slacky1965/air_quality_monitor_zrd/doc/images/screen90.jpg

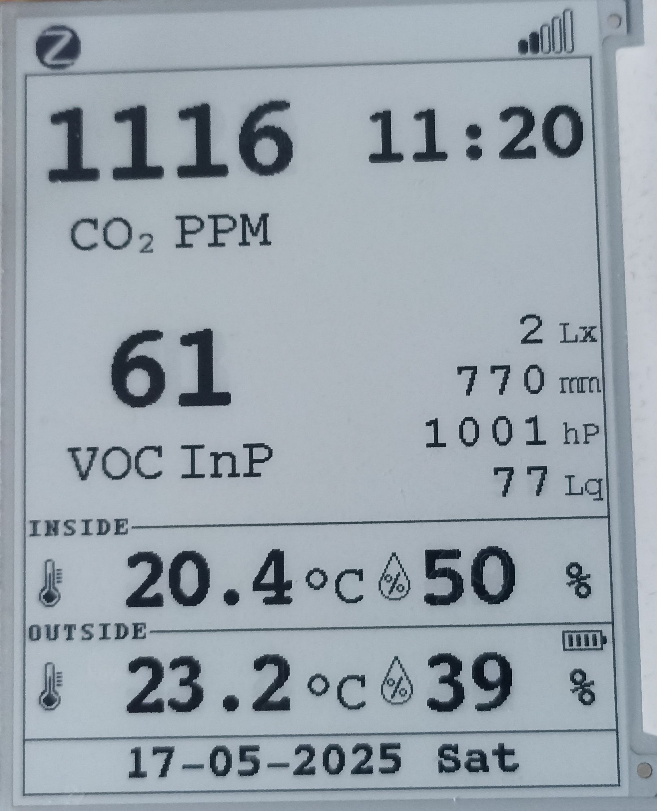
doc/images/screen90.jpg
