slacky1965/air_quality_monitor_zrd/doc/images/z2m_exposes_set1.jpg

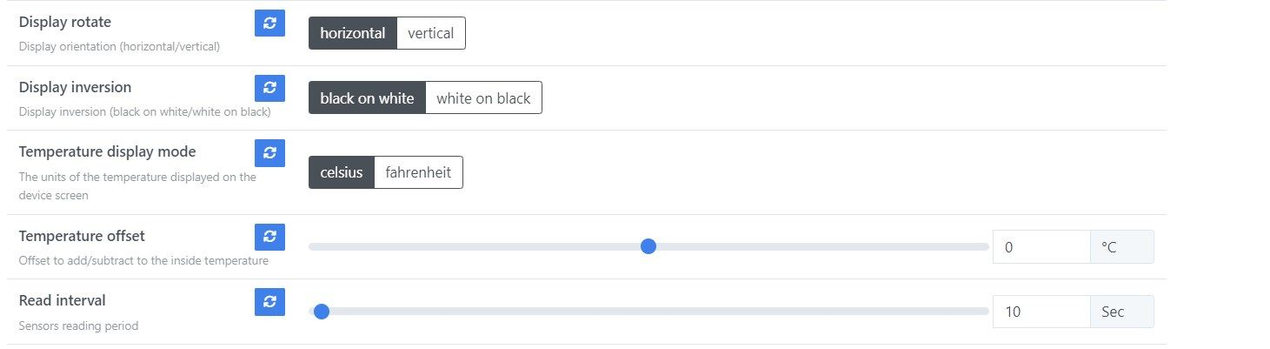
doc/images/z2m_exposes_set1.jpg
