slacky1965/air_quality_monitor_zrd/src/epaper/roboto_font30.c

#include "epdfont.h"

//
//  Font data for Roboto 30pt
//

// Character bitmaps for Roboto 30pt
const uint8_t roboto_font30_Table[] =
{
    // @0 ' ' (33 pixels wide)
    0x00, 0x00, 0x00, 0x00, 0x00, //
    0x00, 0x00, 0x00, 0x00, 0x00, //
    0x00, 0x00, 0x00, 0x00, 0x00, //
    0x00, 0x00, 0x00, 0x00, 0x00, //
    0x00, 0x00, 0x00, 0x00, 0x00, //
    0x00, 0x00, 0x00, 0x00, 0x00, //
    0x00, 0x00, 0x00, 0x00, 0x00, //
    0x00, 0x00, 0x00, 0x00, 0x00, //
    0x00, 0x00, 0x00, 0x00, 0x00, //
    0x00, 0x00, 0x00, 0x00, 0x00, //
    0x00, 0x00, 0x00, 0x00, 0x00, //
    0x00, 0x00, 0x00, 0x00, 0x00, //
    0x00, 0x00, 0x00, 0x00, 0x00, //
    0x00, 0x00, 0x00, 0x00, 0x00, //
    0x00, 0x00, 0x00, 0x00, 0x00, //
    0x00, 0x00, 0x00, 0x00, 0x00, //
    0x00, 0x00, 0x00, 0x00, 0x00, //
    0x00, 0x00, 0x00, 0x00, 0x00, //
    0x00, 0x00, 0x00, 0x00, 0x00, //
    0x00, 0x00, 0x00, 0x00, 0x00, //
    0x00, 0x00, 0x00, 0x00, 0x00, //
    0x00, 0x00, 0x00, 0x00, 0x00, //
    0x00, 0x00, 0x00, 0x00, 0x00, //
    0x00, 0x00, 0x00, 0x00, 0x00, //
    0x00, 0x00, 0x00, 0x00, 0x00, //
    0x00, 0x00, 0x00, 0x00, 0x00, //
    0x00, 0x00, 0x00, 0x00, 0x00, //
    0x00, 0x00, 0x00, 0x00, 0x00, //
    0x00, 0x00, 0x00, 0x00, 0x00, //
    0x00, 0x00, 0x00, 0x00, 0x00, //
    0x00, 0x00, 0x00, 0x00, 0x00, //
    0x00, 0x00, 0x00, 0x00, 0x00, //
    0x00, 0x00, 0x00, 0x00, 0x00, //
    0x00, 0x00, 0x00, 0x00, 0x00, //
    0x00, 0x00, 0x00, 0x00, 0x00, //
    0x00, 0x00, 0x00, 0x00, 0x00, //
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
    0x00, 0x00, 0x00, 0x00, 0x00, //
    0x00, 0x00, 0x00, 0x00, 0x00, //
    0x00, 0x00, 0x00, 0x00, 0x00, //
    0x00, 0x00, 0x00, 0x00, 0x00, //
    0x00, 0x00, 0x00, 0x00, 0x00, //
    0x00, 0x00, 0x00, 0x00, 0x00, //
    0x00, 0x00, 0x00, 0x00, 0x00, //
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
