slacky1965/air_quality_monitor_zrd/src/zcl_appCb.c

/********************************************************************************************************
 * @file    zcl_appCb.c
 *
 * @brief   This is the source file for zcl_appCb
 *
 * @author  Zigbee Group
 * @date    2021
 *
 * @par     Copyright (c) 2021, Telink Semiconductor (Shanghai) Co., Ltd. ("TELINK")
 *			All rights reserved.
 *
 *          Licensed under the Apache License, Version 2.0 (the "License");
 *          you may not use this file except in compliance with the License.
 *          You may obtain a copy of the License at
 *
 *              http://www.apache.org/licenses/LICENSE-2.0
 *
 *          Unless required by applicable law or agreed to in writing, software
 *          distributed under the License is distributed on an "AS IS" BASIS,
 *          WITHOUT WARRANTIES OR CONDITIONS OF ANY KIND, either express or implied.
 *          See the License for the specific language governing permissions and
 *          limitations under the License.
 *
 *******************************************************************************************************/

/**********************************************************************
 * INCLUDES
 */
#include "tl_common.h"
#include "zcl_include.h"

#include "app_main.h"


/**********************************************************************
 * LOCAL CONSTANTS
 */


/**********************************************************************
 * TYPEDEFS
 */


/**********************************************************************
 * LOCAL FUNCTIONS
 */
#ifdef ZCL_READ
static void app_zclReadRspCmd(uint16_t clusterId, zclReadRspCmd_t *pReadRspCmd);
#endif
#ifdef ZCL_WRITE
static void app_zclWriteRspCmd(uint16_t clusterId, zclWriteRspCmd_t *pWriteRspCmd);
static void app_zclWriteReqCmd(uint8_t endPoint, uint16_t clusterId, zclWriteCmd_t *pWriteReqCmd);
#endif
#ifdef ZCL_REPORT
static void app_zclCfgReportCmd(uint8_t endPoint, uint16_t clusterId, zclCfgReportCmd_t *pCfgReportCmd);
static void app_zclCfgReportRspCmd(uint16_t clusterId, zclCfgReportRspCmd_t *pCfgReportRspCmd);
static void app_zclReportCmd(uint16_t clusterId, zclReportCmd_t *pReportCmd, aps_data_ind_t aps_data_ind);
#endif
static void app_zclDfltRspCmd(uint16_t clusterId, zclDefaultRspCmd_t *pDftRspCmd);
static void app_displayMoveToLevelProcess(uint8_t endpoint, uint8_t cmdId, moveToLvl_t *cmd);

/**********************************************************************
 * GLOBAL VARIABLES
 */


/**********************************************************************
 * LOCAL VARIABLES
 */
#ifdef ZCL_IDENTIFY
static ev_timer_event_t *identifyTimerEvt = NULL;
#endif

/**********************************************************************
 * FUNCTIONS
 */

/*********************************************************************
 * @fn      app_zclProcessIncomingMsg
 *
 * @brief   Process ZCL Foundation incoming message.
 *
 * @param   pInMsg - pointer to the received message
 *
 * @return  None
 */
void app_zclProcessIncomingMsg(zclIncoming_t *pInHdlrMsg)
{
//    printf("app_zclProcessIncomingMsg(). hdr.cmd: 0x%x\r\n", pInHdlrMsg->hdr.cmd);

	uint16_t cluster = pInHdlrMsg->msg->indInfo.cluster_id;
	uint8_t endPoint = pInHdlrMsg->msg->indInfo.dst_ep;
	aps_data_ind_t aps_data_ind = pInHdlrMsg->msg->indInfo;
//	uint16_t addr = pInHdlrMsg->msg->indInfo.src_short_addr;

	switch(pInHdlrMsg->hdr.cmd)
	{
#ifdef ZCL_READ
		case ZCL_CMD_READ_RSP:
			app_zclReadRspCmd(cluster, pInHdlrMsg->attrCmd);
			break;
#endif
#ifdef ZCL_WRITE
		case ZCL_CMD_WRITE_RSP:
			app_zclWriteRspCmd(cluster, pInHdlrMsg->attrCmd);
			break;
		case ZCL_CMD_WRITE:
		    app_zclWriteReqCmd(endPoint, cluster, pInHdlrMsg->attrCmd);
			break;
#endif
#ifdef ZCL_REPORT
		case ZCL_CMD_CONFIG_REPORT:
			app_zclCfgReportCmd(endPoint, cluster, pInHdlrMsg->attrCmd);
			break;
		case ZCL_CMD_CONFIG_REPORT_RSP:
			app_zclCfgReportRspCmd(cluster, pInHdlrMsg->attrCmd);
			break;
		case ZCL_CMD_REPORT:
			app_zclReportCmd(cluster, pInHdlrMsg->attrCmd, aps_data_ind);
			break;
#endif
		case ZCL_CMD_DEFAULT_RSP:
			app_zclDfltRspCmd(cluster, pInHdlrMsg->attrCmd);
			break;
		default:
			break;
	}
}

#ifdef ZCL_READ
/*********************************************************************
 * @fn      app_zclReadRspCmd
 *
 * @brief   Handler for ZCL Read Response command.
 *
 * @param   pInHdlrMsg - incoming message to process
 *
 * @return  None
 */
static void app_zclReadRspCmd(uint16_t clusterId, zclReadRspCmd_t *pReadRspCmd)
{
//    printf("app_zclReadRspCmd\r\n");
    uint8_t numAttr = pReadRspCmd->numAttr;
    zclReadRspStatus_t *attrList = pReadRspCmd->attrList;

//    uint32_t utc;
    uint32_t time_local;
    bool time_sent = false;

    for (uint8_t i = 0; i < numAttr; i++) {
///*        if (attrList[i].attrID == ZCL_ATTRID_TIME && attrList[i].status == ZCL_STA_SUCCESS) {
//            utc = attrList[i].data[0] & 0xff;
//            utc |= (attrList[i].data[1] << 8)  & 0x0000ffff;
//            utc |= (attrList[i].data[2] << 16) & 0x00ffffff;
//            utc |= (attrList[i].data[3] << 24) & 0xffffffff;
//            zcl_setAttrVal(APP_ENDPOINT1, ZCL_CLUSTER_GEN_TIME, ZCL_ATTRID_TIME, (uint8_t*)&utc);
//            time_sent = true;
//#if UART_PRINTF_MODE && DEBUG_TIME
//            printf("Sync UTC:        %d\r\n", utc+UNIX_TIME_CONST);
//#endif
//        } else */
        if (attrList[i].attrID == ZCL_ATTRID_LOCAL_TIME && attrList[i].status == ZCL_STA_SUCCESS) {
            time_local = attrList[i].data[0] & 0xff;
            time_local |= (attrList[i].data[1] << 8)  & 0x0000ffff;
            time_local |= (attrList[i].data[2] << 16) & 0x00ffffff;
            time_local |= (attrList[i].data[3] << 24) & 0xffffffff;
            zcl_setAttrVal(APP_ENDPOINT1, ZCL_CLUSTER_GEN_TIME, ZCL_ATTRID_LOCAL_TIME, (uint8_t*)&time_local);
            time_sent = true;
#if UART_PRINTF_MODE && DEBUG_TIME
            printf("Sync Local Time: %d\r\n", time_local+UNIX_TIME_CONST);
#endif
            ftime_t *ft = get_ftime(time_local);
            ds3231_time_t t;
            if (app_ds3231_get_time(&t) == DS3231_OK) {
                t.year = ft->year;
                t.month = ft->month;
                t.week = ft->wday + 1;
                t.date = ft->day;
                t.hour = ft->hour;
                t.minute = ft->minute;
                t.second = ft->second;
                app_ds3231_set_time(&t);
            }
        }
    }

    if (time_sent) {
        set_time_sent();
    }
}
#endif	/* ZCL_READ */

#ifdef ZCL_WRITE
/*********************************************************************
 * @fn      app_zclWriteRspCmd
 *
 * @brief   Handler for ZCL Write Response command.
 *
 * @param   pInHdlrMsg - incoming message to process
 *
 * @return  None
 */
static void app_zclWriteRspCmd(uint16_t clusterId, zclWriteRspCmd_t *pWriteRspCmd)
{
//    printf("app_zclWriteRspCmd\r\n");

}

/*********************************************************************
 * @fn      app_zclWriteReqCmd
 *
 * @brief   Handler for ZCL Write Request command.
 *
 * @param   pInHdlrMsg - incoming message to process
 *
 * @return  None
 */
static void app_zclWriteReqCmd(uint8_t endPoint, uint16_t clusterId, zclWriteCmd_t *pWriteReqCmd) {
    uint8_t numAttr = pWriteReqCmd->numAttr;
    zclWriteRec_t *attr = pWriteReqCmd->attrList;

    uint8_t val;
    bool save = false;

//    printf("app_zclWriteReqCmd. cluster: 0x%04x\r\n", clusterId);

    if (clusterId == ZCL_CLUSTER_GEN_LEVEL_CONTROL) {
        for (uint16_t i = 0; i < numAttr; i++) {
            if (attr[i].attrID == ZCL_ATTRID_LEVEL_CURRENT_LEVEL) {
                moveToLvl_t cmd;
                cmd.level = attr[i].attrData[0];
                app_displayMoveToLevelProcess(endPoint, ZCL_CMD_LEVEL_MOVE_TO_LEVEL, &cmd);
            }
        }
    }


    if (clusterId == ZCL_CLUSTER_HAVC_USER_INTERFACE_CONFIG) {
        for (uint16_t i = 0; i < numAttr; i++) {
            if (attr[i].attrID == ZCL_ATTRID_HVAC_TEMPERATURE_DISPLAY_MODE) {
                val = attr[i].attrData[0];
                if (val == 0 || val == 1) {
                    printf("Set %s\r\n", val?"Fahrenheit":"Celsius");
                    if (config.d_mode != val) {
                        config.d_mode = val;
                        save = true;
                        epd_update_temperature_display_mode();
                    }
                }
            } else if (attr[i].attrID == ZCL_ATTRID_HVAC_CUSTOM_DISPLAY_ROTATE) {
                val = attr[i].attrData[0];
                if (val == 0 || val == 1) {
                    printf("Rotate set: %s\r\n", val?"Vertical":"Horizontal");
                    if (config.rotate != val) {
                        config.rotate = val;
                        save = true;
                        TL_SCHEDULE_TASK(epd_forceScreenUpdate, NULL);
                    }
                }
            } else if (attr[i].attrID == ZCL_ATTRID_HVAC_CUSTOM_DISPLAY_INVERSION) {
                val = attr[i].attrData[0];
                if (val == 0 || val == 1) {
                    printf("Inversion set: %s\r\n", val?"Black on white":"White on black");
                    if (config.inversion != val) {
                        config.inversion = val;
                        save = true;
                        TL_SCHEDULE_TASK(epd_forceScreenUpdate, NULL);
                    }
                }
            } else if (attr[i].attrID == ZCL_ATTRID_HVAC_CUSTOM_SOUND) {
                val = attr[i].attrData[0];
                if (val == 0 || val == 1) {
                    printf("Sound set: %s\r\n", val?"On":"Off");
                    if (config.sound != val) {
                        config.sound = val;
                        sound_start(4, 20, 100, val?SOUND_INC:SOUND_DEC);
                        epd_screen_varCb(NULL);
                        save = true;
                    }
                }
            } else if (attr[i].attrID == ZCL_ATTRID_HVAC_CUSTOM_FEATURES_SENSORS) {
                uint8_t ret;
                if (attr[i].attrData[0] == FEATURES_CO2_FORCED_CALIBRATION &&
                        !g_appCtx.co2_forced_calibration &&
                        !g_appCtx.co2_factory_reset) {
                    g_appCtx.co2_forced_calibration = 1;
                    ret = app_scd4x_forced_calibration();
                    printf("CO2 calibration: %d, ret: %d\r\n", attr[i].attrData[0], ret);
                } else if (attr[i].attrData[0] == FEATURES_CO2_FACTORY_RESET &&
                        !g_appCtx.co2_factory_reset &&
                        !g_appCtx.co2_forced_calibration) {
                    g_appCtx.co2_factory_reset = 1;
                    ret = app_scd4x_factory_reset();
                    printf("CO2 factory reset: %d, ret: %d\r\n", attr[i].attrData[0], ret);
                } else if (attr[i].attrData[0] == FEATURES_BIND_RESET) {
                    printf("Bind reset: %d\r\n", attr[i].attrData[0]);
                    bind_outside_init();
                }
                uint8_t attrFeatures = 0;
                zcl_setAttrVal(APP_ENDPOINT1, ZCL_CLUSTER_HAVC_USER_INTERFACE_CONFIG,
                               ZCL_ATTRID_HVAC_CUSTOM_FEATURES_SENSORS, (uint8_t*)&attrFeatures);
            }
        }
    }

    if (clusterId == ZCL_CLUSTER_MS_TEMPERATURE_MEASUREMENT) {
        for (uint16_t i = 0; i < numAttr; i++) {
            if (attr[i].attrID == ZCL_ATTRID_TMS_CUSTOM_TEMPERATURE_OFFSET) {
                int16_t temp = attr[i].attrData[0] & 0xff;
                temp |= (attr[i].attrData[1] << 8) & 0xffff;
//                printf("Temperature offset: %d\r\n", temp);
                if (temp >= TEMPERATURE_OFFSET_MIN && temp <= TEMPERATURE_OFFSET_MAX) {
                    if (temp != config.temperature_offset) {
                        config.temperature_offset = temp;
                        save = true;
                    }
                }
                epd_update_temperature_display_mode();
            } else if (attr[i].attrID == ZCL_ATTRID_TMS_CUSTOM_READ_SENSORS_PERIOD) {
                uint16_t ms_period = attr[i].attrData[0] & 0xff;
                ms_period |= (attr[i].attrData[1] << 8) & 0xffff;
                if (ms_period >= READ_SENSORS_PERIOD_MIN && ms_period <= READ_SENSORS_PERIOD_MAX) {
                    if (ms_period != config.read_sensors_period) {
                        config.read_sensors_period = ms_period;
                        save = true;
                        if (g_appCtx.timerMesurementEvt) {
                            TL_ZB_TIMER_CANCEL(&g_appCtx.timerMesurementEvt);
                        }
                        g_appCtx.timerMesurementEvt = TL_ZB_TIMER_SCHEDULE(app_mesurementCb, NULL, TIMEOUT_100MS);
                    }
                }
            }
        }
    }

    if (clusterId == ZCL_CLUSTER_GEN_ANALOG_INPUT_BASIC) {
        for (uint16_t i = 0; i < numAttr; i++) {
            if (attr[i].attrID == ZCL_ATTRID_AI_CUSTOM_VOC_ONOFF) {
                if (config.voc_onoff != attr[i].attrData[0]) {
                    config.voc_onoff = attr[i].attrData[0];
                    save = true;
//                    printf("VOC onoff: %d\r\n", config.voc_onoff);
                }
            } else if (attr[i].attrID == ZCL_ATTRID_AI_CUSTOM_VOC_LOW) {
                uint16_t voc_low = attr[i].attrData[0] & 0xff;
                voc_low |= (attr[i].attrData[1] << 8) & 0xffff;
                if (voc_low >= VOC_ONOFF_MIN && voc_low <= VOC_ONOFF_MAX) {
                    if (voc_low < config.voc_onoff_high) {
                        if (config.voc_onoff_low != voc_low) {
                            config.voc_onoff_low = voc_low;
                            save = true;
//                            printf("VOC low: %d\r\n", config.voc_onoff_low);
                        }
                    } else {
                        zcl_setAttrVal(APP_ENDPOINT1,
                                       ZCL_CLUSTER_GEN_ANALOG_INPUT_BASIC,
                                       ZCL_ATTRID_AI_CUSTOM_VOC_LOW,
                                       (uint8_t*)&config.voc_onoff_low);
                    }
                }
            } else if (attr[i].attrID == ZCL_ATTRID_AI_CUSTOM_VOC_HIGH) {
                uint16_t voc_high = attr[i].attrData[0] & 0xff;
                voc_high |= (attr[i].attrData[1] << 8) & 0xffff;
                if (voc_high >= VOC_ONOFF_MIN && voc_high <= VOC_ONOFF_MAX) {
                    if (voc_high > config.voc_onoff_low) {
                        if (config.voc_onoff_high != voc_high) {
                            config.voc_onoff_high = voc_high;
                            save = true;
//                            printf("VOC high: %d\r\n", config.voc_onoff_high);
                        }
                    } else {
                        zcl_setAttrVal(APP_ENDPOINT1,
                                       ZCL_CLUSTER_GEN_ANALOG_INPUT_BASIC,
                                       ZCL_ATTRID_AI_CUSTOM_VOC_HIGH,
                                       (uint8_t*)&config.voc_onoff_high);
                    }
                }
            }
        }
    }

    if (clusterId == ZCL_CLUSTER_MS_CO2_MEASUREMENT) {
        for (uint16_t i = 0; i < numAttr; i++) {
            if (attr[i].attrID == ZCL_ATTRID_CMS_CUSTOM_CO2_ONOFF) {
                if (config.co2_onoff != attr[i].attrData[0]) {
                    config.co2_onoff = attr[i].attrData[0];
                    save = true;
//                    printf("CO2 onoff: %d\r\n", config.co2_onoff);
                }
            } else if (attr[i].attrID == ZCL_ATTRID_CMS_CUSTOM_CO2_LOW) {
                uint16_t co2_low = attr[i].attrData[0] & 0xff;
                co2_low |= (attr[i].attrData[1] << 8) & 0xffff;
                if (co2_low >= CO2_ONOFF_MIN && co2_low <= CO2_ONOFF_MAX) {
                    if (co2_low < config.co2_onoff_high) {
                        if (config.co2_onoff_low != co2_low) {
                            config.co2_onoff_low = co2_low;
                            save = true;
//                            printf("CO2 low: %d\r\n", config.co2_onoff_low);
                        }
                    } else {
                        zcl_setAttrVal(APP_ENDPOINT1,
                                       ZCL_CLUSTER_MS_CO2_MEASUREMENT,
                                       ZCL_ATTRID_CMS_CUSTOM_CO2_LOW,
                                       (uint8_t*)&config.co2_onoff_low);
                    }
                }
            } else if (attr[i].attrID == ZCL_ATTRID_CMS_CUSTOM_CO2_HIGH) {
                uint16_t co2_high = attr[i].attrData[0] & 0xff;
                co2_high |= (attr[i].attrData[1] << 8) & 0xffff;
                if (co2_high >= CO2_ONOFF_MIN && co2_high <= CO2_ONOFF_MAX) {
                    if (co2_high > config.co2_onoff_low) {
                        if (config.co2_onoff_high != co2_high) {
                            config.co2_onoff_high = co2_high;
                            save = true;
//                            printf("CO2 high: %d\r\n", config.co2_onoff_high);
                        }
                    } else {
                        zcl_setAttrVal(APP_ENDPOINT1,
                                       ZCL_CLUSTER_MS_CO2_MEASUREMENT,
                                       ZCL_ATTRID_CMS_CUSTOM_CO2_HIGH,
                                       (uint8_t*)&config.co2_onoff_high);
                    }
                }
            }
        }
    }

    if (clusterId == ZCL_CLUSTER_GEN_ON_OFF_SWITCH_CONFIG) {
        for (u8 i = 0; i < numAttr; i++) {
            if (attr[i].attrID == ZCL_ATTRID_SWITCH_ACTION) {
                zcl_onOffCfgAttr_save();
            }
        }
    }

    if (save)
        config_save();

#ifdef ZCL_POLL_CTRL
	if(clusterId == ZCL_CLUSTER_GEN_POLL_CONTROL){
		for(int32_t i = 0; i < numAttr; i++){
			if(attr[i].attrID == ZCL_ATTRID_CHK_IN_INTERVAL){
				app_zclCheckInStart();
				return;
			}
		}
	}
#endif

}
#endif	/* ZCL_WRITE */


/*********************************************************************
 * @fn      app_zclDfltRspCmd
 *
 * @brief   Handler for ZCL Default Response command.
 *
 * @param   pInHdlrMsg - incoming message to process
 *
 * @return  None
 */
static void app_zclDfltRspCmd(uint16_t clusterId, zclDefaultRspCmd_t *pDftRspCmd)
{
//    printf("app_zclDfltRspCmd\r\n");

}

#ifdef ZCL_REPORT
/*********************************************************************
 * @fn      app_zclCfgReportCmd
 *
 * @brief   Handler for ZCL Configure Report command.
 *
 * @param   pInHdlrMsg - incoming message to process
 * @param   dst_ep     - number of endPoint
 *
 * @return  None
 */
static void app_zclCfgReportCmd(uint8_t endPoint, uint16_t clusterId, zclCfgReportCmd_t *pCfgReportCmd)
{
//    printf("app_zclCfgReportCmd\r\n");

    reportAttrTimerStop();


//    for(uint8_t i = 0; i < pCfgReportCmd->numAttr; i++) {
//        printf("direction: %d, attrId: 0x%04x\r\n",
//                pCfgReportCmd->attrList[i].direction,
//                pCfgReportCmd->attrList[i].attrID);
//    }
}

/*********************************************************************
 * @fn      app_zclCfgReportRspCmd
 *
 * @brief   Handler for ZCL Configure Report Response command.
 *
 * @param   pInHdlrMsg - incoming message to process
 *
 * @return  None
 */
static void app_zclCfgReportRspCmd(uint16_t clusterId, zclCfgReportRspCmd_t *pCfgReportRspCmd)
{
//    printf("app_zclCfgReportRspCmd\r\n");

}

/*********************************************************************
 * @fn      app_zclReportCmd
 *
 * @brief   Handler for ZCL Report command.
 *
 * @param   pInHdlrMsg - incoming message to process
 *
 * @return  None
 */
static void app_zclReportCmd(uint16_t clusterId, zclReportCmd_t *pReportCmd, aps_data_ind_t aps_data_ind) {
//    printf("app_zclReportCmd\r\n");

    uint8_t numAttr = pReportCmd->numAttr;
    zclReport_t *attrList = pReportCmd->attrList;

    uint8_t ret;
    uint16_t addr = aps_data_ind.src_short_addr;

    for (uint8_t i = 0; i < numAttr; i++) {
        if (clusterId == ZCL_CLUSTER_MS_TEMPERATURE_MEASUREMENT &&
                attrList[i].dataType == ZCL_DATA_TYPE_INT16 &&
                attrList[i].attrID == ZCL_TEMPERATURE_MEASUREMENT_ATTRID_MEASUREDVALUE) {
            int16_t temp;

            temp = attrList[i].attrData[0] & 0xFF;
            temp |= (attrList[i].attrData[1] << 8) & 0xFFFF;

//            printf("temp: 0x%04x\r\n", (uint16_t)temp);

            ret = bind_outsise_proc(addr, clusterId);

            if (ret != OUTSIDE_SRC_CLUSTER_OK) {
                continue;
            }

            app_set_outside_temperature(temp);
            bind_outside_update_timer();
        }
        if (clusterId == ZCL_CLUSTER_MS_RELATIVE_HUMIDITY &&
                attrList[i].dataType == ZCL_DATA_TYPE_UINT16 &&
                attrList[i].attrID == ZCL_ATTRID_HUMIDITY_MEASUREDVALUE) {
            uint16_t hum;

            hum = attrList[i].attrData[0] & 0xFF;
            hum |= (attrList[i].attrData[1] << 8) & 0xFFFF;

//            printf("hum: 0x%04x\r\n", hum);

            ret = bind_outsise_proc(addr, clusterId);

            if (ret != OUTSIDE_SRC_CLUSTER_OK) {
                continue;
            }

            app_set_outside_humidity(hum);
            bind_outside_update_timer();
        }
        if (clusterId == ZCL_CLUSTER_GEN_POWER_CFG &&
                attrList[i].dataType == ZCL_DATA_TYPE_UINT8 &&
                attrList[i].attrID == ZCL_ATTRID_BATTERY_PERCENTAGE_REMAINING) {
            uint8_t bat_percent = attrList[i].attrData[0];

            ret = bind_outsise_proc(addr, clusterId);

            if (ret != OUTSIDE_SRC_CLUSTER_OK) {
                continue;
            }

            app_set_outside_battery(bat_percent);
            bind_outside_update_timer();
        }
    }
}
#endif	/* ZCL_REPORT */

#ifdef ZCL_BASIC
/*********************************************************************
 * @fn      app_zclBasicResetCmdHandler
 *
 * @brief   Handler for ZCL Basic Reset command.
 *
 * @param   pAddrInfo
 * @param   cmdId
 * @param   cmdPayload
 *
 * @return  status_t
 */
status_t app_basicCb(zclIncomingAddrInfo_t *pAddrInfo, uint8_t cmdId, void *cmdPayload)
{
	if(cmdId == ZCL_CMD_BASIC_RESET_FAC_DEFAULT){
		//Reset all the attributes of all its clusters to factory defaults
		//zcl_nv_attr_reset();
	}

	return ZCL_STA_SUCCESS;
}
#endif	/* ZCL_BASIC */

#ifdef ZCL_IDENTIFY
int32_t app_zclIdentifyTimerCb(void *arg)
{
	if(g_zcl_identifyAttrs.identifyTime <= 0) {
	    g_appCtx.bdbFindBindFlg = false;
		identifyTimerEvt = NULL;
		return -1;
	}
	g_zcl_identifyAttrs.identifyTime--;
	return 0;
}

void app_zclIdentifyTimerStop(void)
{
    g_appCtx.bdbFindBindFlg = false;
	if(identifyTimerEvt){
		TL_ZB_TIMER_CANCEL(&identifyTimerEvt);
	}
}

/*********************************************************************
 * @fn      app_zclIdentifyCmdHandler
 *
 * @brief   Handler for ZCL Identify command. This function will set blink LED.
 *
 * @param   endpoint
 * @param   srcAddr
 * @param   identifyTime - identify time
 *
 * @return  None
 */
void app_zclIdentifyCmdHandler(uint8_t endpoint, uint16_t srcAddr, uint16_t identifyTime) {

	g_zcl_identifyAttrs.identifyTime = identifyTime;

	if(identifyTime == 0) {
		app_zclIdentifyTimerStop();
		led_blink_stop();
	}else{
		if(!identifyTimerEvt) {
//	        led_effect_start(90, COLOR_GREEN);
	        led_blink_start(identifyTime, 500, 500, COLOR_GREEN);
			identifyTimerEvt = TL_ZB_TIMER_SCHEDULE(app_zclIdentifyTimerCb, NULL, 1000);
		}
	}
}

/*********************************************************************
 * @fn      app_zcltriggerCmdHandler
 *
 * @brief   Handler for ZCL trigger command.
 *
 * @param   pTriggerEffect
 *
 * @return  None
 */
static void app_zcltriggerCmdHandler(zcl_triggerEffect_t *pTriggerEffect)
{
	uint8_t effectId = pTriggerEffect->effectId;
	//uint8_t effectVariant = pTriggerEffect->effectVariant;

	switch(effectId){
		case IDENTIFY_EFFECT_BLINK:
//			light_blink_start(1, 500, 500);
			break;
		case IDENTIFY_EFFECT_BREATHE:
//			light_blink_start(15, 300, 700);
			break;
		case IDENTIFY_EFFECT_OKAY:
//			light_blink_start(2, 250, 250);
			break;
		case IDENTIFY_EFFECT_CHANNEL_CHANGE:
//			light_blink_start(1, 500, 7500);
			break;
		case IDENTIFY_EFFECT_FINISH_EFFECT:
//			light_blink_start(1, 300, 700);
			break;
		case IDENTIFY_EFFECT_STOP_EFFECT:
//			light_blink_stop();
			break;
		default:
			break;
	}
}

/*********************************************************************
 * @fn      app_zclIdentifyQueryRspCmdHandler
 *
 * @brief   Handler for ZCL Identify Query response command.
 *
 * @param   endpoint
 * @param   srcAddr
 * @param   identifyRsp
 *
 * @return  None
 */
static void app_zclIdentifyQueryRspCmdHandler(uint8_t endpoint, uint16_t srcAddr, zcl_identifyRspCmd_t *identifyRsp)
{
#if FIND_AND_BIND_SUPPORT
	if(identifyRsp->timeout){
		findBindDst_t dstInfo;
		dstInfo.addr = srcAddr;
		dstInfo.endpoint = endpoint;

		bdb_addIdentifyActiveEpForFB(dstInfo);
	}
#endif
}

/*********************************************************************
 * @fn      app_identifyCb
 *
 * @brief   Handler for ZCL Identify command.
 *
 * @param   pAddrInfo
 * @param   cmdId
 * @param   cmdPayload
 *
 * @return  status_t
 */
status_t app_identifyCb(zclIncomingAddrInfo_t *pAddrInfo, uint8_t cmdId, void *cmdPayload)
{

//    printf("app_identifyCb()\r\n");

	if(pAddrInfo->dstEp == APP_ENDPOINT1){
		if(pAddrInfo->dirCluster == ZCL_FRAME_CLIENT_SERVER_DIR){
			switch(cmdId){
				case ZCL_CMD_IDENTIFY:
					app_zclIdentifyCmdHandler(pAddrInfo->dstEp, pAddrInfo->srcAddr, ((zcl_identifyCmd_t *)cmdPayload)->identifyTime);
					break;
				case ZCL_CMD_TRIGGER_EFFECT:
					app_zcltriggerCmdHandler((zcl_triggerEffect_t *)cmdPayload);
					break;
				default:
					break;
			}
		}else{
			if(cmdId == ZCL_CMD_IDENTIFY_QUERY_RSP){
				app_zclIdentifyQueryRspCmdHandler(pAddrInfo->dstEp, pAddrInfo->srcAddr, (zcl_identifyRspCmd_t *)cmdPayload);
			}
		}
	}

	return ZCL_STA_SUCCESS;
}
#endif	/* ZCL_IDENTIFY */

#ifdef ZCL_IAS_ZONE
/*********************************************************************
 * @fn      leak_zclIasZoneEnrollRspCmdHandler
 *
 * @brief   Handler for ZCL IAS ZONE Enroll response command.
 *
 * @param   pZoneEnrollRsp
 *
 * @return  None
 */
static void leak_zclIasZoneEnrollRspCmdHandler(zoneEnrollRsp_t *pZoneEnrollRsp, uint8_t endpoint) {

    //printf("zclIasZoneEnrollRspCmdHandler endpoint: %d, code: %d zone_id: %d\r\n", endpoint, pZoneEnrollRsp->code, pZoneEnrollRsp->zoneId);
    if (pZoneEnrollRsp->zoneId != ZCL_ZONE_ID_INVALID) {
        u8 zoneState;
        zoneState = ZONE_STATE_ENROLLED;
        zcl_setAttrVal(endpoint, ZCL_CLUSTER_SS_IAS_ZONE, ZCL_ATTRID_ZONE_ID, &(pZoneEnrollRsp->zoneId));
        zcl_setAttrVal(endpoint, ZCL_CLUSTER_SS_IAS_ZONE, ZCL_ATTRID_ZONE_STATE, &zoneState);
    }

}

/*********************************************************************
 * @fn      leak_zclIasZoneInitNormalOperationModeCmdHandler
 *
 * @brief   Handler for ZCL IAS ZONE normal operation mode command.
 *
 * @param
 *
 * @return  status
 */
static status_t leak_zclIasZoneInitNormalOperationModeCmdHandler(void) {

    //printf("zclIasZoneInitNormalOperationModeCmdHandler\r\n");
    u8 status = ZCL_STA_FAILURE;

    return status;
}

/*********************************************************************
 * @fn      leak_zclIasZoneInitTestModeCmdHandler
 *
 * @brief   Handler for ZCL IAS ZONE test mode command.
 *
 * @param   pZoneInitTestMode
 *
 * @return  status
 */
static status_t leak_zclIasZoneInitTestModeCmdHandler(zoneInitTestMode_t *pZoneInitTestMode) {

    //printf("zclIasZoneInitNormalOperationModeCmdHandler\r\n");
    u8 status = ZCL_STA_FAILURE;

    return status;
}

/*********************************************************************
 * @fn      leak_iasZoneCb
 *
 * @brief   Handler for ZCL IAS Zone command.
 *
 * @param   pAddrInfo
 * @param   cmdId
 * @param   cmdPayload
 *
 * @return  status_t
 */
status_t leak_iasZoneCb(zclIncomingAddrInfo_t *pAddrInfo, u8 cmdId, void *cmdPayload)
{
    status_t status = ZCL_STA_SUCCESS;

    if(pAddrInfo->dstEp == APP_ENDPOINT4 || pAddrInfo->dstEp == APP_ENDPOINT5){
        if(pAddrInfo->dirCluster == ZCL_FRAME_CLIENT_SERVER_DIR){
            switch(cmdId){
                case ZCL_CMD_ZONE_ENROLL_RSP:
                    leak_zclIasZoneEnrollRspCmdHandler((zoneEnrollRsp_t *)cmdPayload, pAddrInfo->dstEp);
                    break;
                case ZCL_CMD_INIT_NORMAL_OPERATION_MODE:
                    leak_zclIasZoneInitNormalOperationModeCmdHandler();
                    break;
                case ZCL_CMD_INIT_TEST_MODE:
                    leak_zclIasZoneInitTestModeCmdHandler((zoneInitTestMode_t *)cmdPayload);
                    break;
                default:
                    break;
            }
        }
    }

    return status;
}
#endif  /* ZCL_IAS_ZONE */


/*********************************************************************
 * @fn      app_powerCfgCb
 *
 * @brief   Handler for ZCL Identify command.
 *
 * @param   pAddrInfo
 * @param   cmdId
 * @param   cmdPayload
 *
 * @return  status_t
 */
status_t app_powerCfgCb(zclIncomingAddrInfo_t *pAddrInfo, uint8_t cmdId, void *cmdPayload)
{

    return ZCL_STA_SUCCESS;
}


#ifdef ZCL_GROUP
/*********************************************************************
 * @fn      app_zclAddGroupRspCmdHandler
 *
 * @brief   Handler for ZCL add group response command.
 *
 * @param   pAddGroupRsp
 *
 * @return  None
 */
static void app_zclAddGroupRspCmdHandler(uint8_t ep, zcl_addGroupRsp_t *pAddGroupRsp) {

//    printf("app_zclAddGroupRspCmdHandler. ep: %d, status: %d, gid: %d\r\n", ep, pAddGroupRsp->status, pAddGroupRsp->groupId);
}

/*********************************************************************
 * @fn      app_zclViewGroupRspCmdHandler
 *
 * @brief   Handler for ZCL view group response command.
 *
 * @param   pViewGroupRsp
 *
 * @return  None
 */
static void app_zclViewGroupRspCmdHandler(zcl_viewGroupRsp_t *pViewGroupRsp)
{

}

/*********************************************************************
 * @fn      app_zclRemoveGroupRspCmdHandler
 *
 * @brief   Handler for ZCL remove group response command.
 *
 * @param   pRemoveGroupRsp
 *
 * @return  None
 */
static void app_zclRemoveGroupRspCmdHandler(zcl_removeGroupRsp_t *pRemoveGroupRsp)
{

}

/*********************************************************************
 * @fn      app_zclGetGroupMembershipRspCmdHandler
 *
 * @brief   Handler for ZCL get group membership response command.
 *
 * @param   pGetGroupMembershipRsp
 *
 * @return  None
 */
static void app_zclGetGroupMembershipRspCmdHandler(zcl_getGroupMembershipRsp_t *pGetGroupMembershipRsp)
{

}

/*********************************************************************
 * @fn      app_groupCb
 *
 * @brief   Handler for ZCL Group command.
 *
 * @param   pAddrInfo
 * @param   cmdId
 * @param   cmdPayload
 *
 * @return  status_t
 */
status_t app_groupCb(zclIncomingAddrInfo_t *pAddrInfo, uint8_t cmdId, void *cmdPayload) {

//    printf("app_groupCb. ep: %d\r\n", pAddrInfo->dstEp);

	if(pAddrInfo->dstEp == APP_ENDPOINT1 || pAddrInfo->dstEp == APP_ENDPOINT2) {
		if(pAddrInfo->dirCluster == ZCL_FRAME_SERVER_CLIENT_DIR){
			switch(cmdId){
				case ZCL_CMD_GROUP_ADD_GROUP_RSP:
					app_zclAddGroupRspCmdHandler(pAddrInfo->dstEp, (zcl_addGroupRsp_t *)cmdPayload);
					break;
				case ZCL_CMD_GROUP_VIEW_GROUP_RSP:
					app_zclViewGroupRspCmdHandler((zcl_viewGroupRsp_t *)cmdPayload);
					break;
				case ZCL_CMD_GROUP_REMOVE_GROUP_RSP:
					app_zclRemoveGroupRspCmdHandler((zcl_removeGroupRsp_t *)cmdPayload);
					break;
				case ZCL_CMD_GROUP_GET_MEMBERSHIP_RSP:
					app_zclGetGroupMembershipRspCmdHandler((zcl_getGroupMembershipRsp_t *)cmdPayload);
					break;
				default:
					break;
			}
		}
	}

	return ZCL_STA_SUCCESS;
}
#endif	/* ZCL_GROUP */

#ifdef ZCL_SCENE
/*********************************************************************
 * @fn      app_zclAddSceneRspCmdHandler
 *
 * @brief   Handler for ZCL add scene response command.
 *
 * @param   cmdId
 * @param   pAddSceneRsp
 *
 * @return  None
 */
static void app_zclAddSceneRspCmdHandler(uint8_t cmdId, addSceneRsp_t *pAddSceneRsp)
{

}

/*********************************************************************
 * @fn      app_zclViewSceneRspCmdHandler
 *
 * @brief   Handler for ZCL view scene response command.
 *
 * @param   cmdId
 * @param   pViewSceneRsp
 *
 * @return  None
 */
static void app_zclViewSceneRspCmdHandler(uint8_t cmdId, viewSceneRsp_t *pViewSceneRsp)
{

}

/*********************************************************************
 * @fn      app_zclRemoveSceneRspCmdHandler
 *
 * @brief   Handler for ZCL remove scene response command.
 *
 * @param   pRemoveSceneRsp
 *
 * @return  None
 */
static void app_zclRemoveSceneRspCmdHandler(removeSceneRsp_t *pRemoveSceneRsp)
{

}

/*********************************************************************
 * @fn      app_zclRemoveAllSceneRspCmdHandler
 *
 * @brief   Handler for ZCL remove all scene response command.
 *
 * @param   pRemoveAllSceneRsp
 *
 * @return  None
 */
static void app_zclRemoveAllSceneRspCmdHandler(removeAllSceneRsp_t *pRemoveAllSceneRsp)
{

}

/*********************************************************************
 * @fn      app_zclStoreSceneRspCmdHandler
 *
 * @brief   Handler for ZCL store scene response command.
 *
 * @param   pStoreSceneRsp
 *
 * @return  None
 */
static void app_zclStoreSceneRspCmdHandler(storeSceneRsp_t *pStoreSceneRsp)
{

}

/*********************************************************************
 * @fn      app_zclGetSceneMembershipRspCmdHandler
 *
 * @brief   Handler for ZCL get scene membership response command.
 *
 * @param   pGetSceneMembershipRsp
 *
 * @return  None
 */
static void app_zclGetSceneMembershipRspCmdHandler(getSceneMemRsp_t *pGetSceneMembershipRsp)
{

}

/*********************************************************************
 * @fn      app_sceneCb
 *
 * @brief   Handler for ZCL Scene command.
 *
 * @param   pAddrInfo
 * @param   cmdId
 * @param   cmdPayload
 *
 * @return  status_t
 */
status_t app_sceneCb(zclIncomingAddrInfo_t *pAddrInfo, uint8_t cmdId, void *cmdPayload)
{
	if(pAddrInfo->dstEp == APP_ENDPOINT1){
		if(pAddrInfo->dirCluster == ZCL_FRAME_SERVER_CLIENT_DIR){
			switch(cmdId){
				case ZCL_CMD_SCENE_ADD_SCENE_RSP:
				case ZCL_CMD_SCENE_ENHANCED_ADD_SCENE_RSP:
					app_zclAddSceneRspCmdHandler(cmdId, (addSceneRsp_t *)cmdPayload);
					break;
				case ZCL_CMD_SCENE_VIEW_SCENE_RSP:
				case ZCL_CMD_SCENE_ENHANCED_VIEW_SCENE_RSP:
					app_zclViewSceneRspCmdHandler(cmdId, (viewSceneRsp_t *)cmdPayload);
					break;
				case ZCL_CMD_SCENE_REMOVE_SCENE_RSP:
					app_zclRemoveSceneRspCmdHandler((removeSceneRsp_t *)cmdPayload);
					break;
				case ZCL_CMD_SCENE_REMOVE_ALL_SCENE_RSP:
					app_zclRemoveAllSceneRspCmdHandler((removeAllSceneRsp_t *)cmdPayload);
					break;
				case ZCL_CMD_SCENE_STORE_SCENE_RSP:
					app_zclStoreSceneRspCmdHandler((storeSceneRsp_t *)cmdPayload);
					break;
				case ZCL_CMD_SCENE_GET_SCENE_MEMSHIP_RSP:
					app_zclGetSceneMembershipRspCmdHandler((getSceneMemRsp_t *)cmdPayload);
					break;
				default:
					break;
			}
		}
	}

	return ZCL_STA_SUCCESS;
}
#endif	/* ZCL_SCENE */

#ifdef ZCL_POLL_CTRL
static ev_timer_event_t *zclFastPollTimeoutTimerEvt = NULL;
static ev_timer_event_t *zclCheckInTimerEvt = NULL;
static bool isFastPollMode = FALSE;

void app_zclCheckInCmdSend(void)
{
	epInfo_t dstEpInfo;
	TL_SETSTRUCTCONTENT(dstEpInfo, 0);

	dstEpInfo.dstAddrMode = APS_DSTADDR_EP_NOTPRESETNT;
	dstEpInfo.dstEp = APP_ENDPOINT;
	dstEpInfo.profileId = HA_PROFILE_ID;

	zcl_pollCtrl_checkInCmd(APP_ENDPOINT, &dstEpInfo, TRUE);
}

int32_t app_zclCheckInTimerCb(void *arg)
{
	zcl_pollCtrlAttr_t *pPollCtrlAttr = zcl_pollCtrlAttrGet();

	if(!pPollCtrlAttr->chkInInterval){
		zclCheckInTimerEvt = NULL;
		return -1;
	}

	app_zclCheckInCmdSend();

	return 0;
}

void app_zclCheckInStart(void)
{
	if(zb_bindingTblSearched(ZCL_CLUSTER_GEN_POLL_CONTROL, APP_ENDPOINT)){
		zcl_pollCtrlAttr_t *pPollCtrlAttr = zcl_pollCtrlAttrGet();

		if(!zclCheckInTimerEvt){
			zclCheckInTimerEvt = TL_ZB_TIMER_SCHEDULE(app_zclCheckInTimerCb, NULL, pPollCtrlAttr->chkInInterval * POLL_RATE_QUARTERSECONDS);
			
			if(pPollCtrlAttr->chkInInterval){
				app_zclCheckInCmdSend();
			}
		}
	}
}

void app_zclSetFastPollMode(bool fastPollMode)
{
	zcl_pollCtrlAttr_t *pPollCtrlAttr = zcl_pollCtrlAttrGet();

	isFastPollMode = fastPollMode;
	uint32_t pollRate = fastPollMode ? pPollCtrlAttr->shortPollInterval : pPollCtrlAttr->longPollInterval;

	zb_setPollRate(pollRate  * POLL_RATE_QUARTERSECONDS);
}

int32_t app_zclFastPollTimeoutCb(void *arg)
{
	app_zclSetFastPollMode(FALSE);

	zclFastPollTimeoutTimerEvt = NULL;
	return -1;
}

static status_t app_zclPollCtrlChkInRspCmdHandler(zcl_chkInRsp_t *pCmd)
{
	zcl_pollCtrlAttr_t *pPollCtrlAttr = zcl_pollCtrlAttrGet();

	if(pCmd->startFastPolling){
		uint16_t fastPollTimeoutCnt = 0;

		if(pCmd->fastPollTimeout){
			if(pCmd->fastPollTimeout > pPollCtrlAttr->fastPollTimeoutMax){
				return ZCL_STA_INVALID_FIELD;
			}

			fastPollTimeoutCnt = pCmd->fastPollTimeout;
		}else{
			fastPollTimeoutCnt = pPollCtrlAttr->fastPollTimeout;
		}

		if(fastPollTimeoutCnt){
			app_zclSetFastPollMode(TRUE);
			
			if(zclFastPollTimeoutTimerEvt){
				TL_ZB_TIMER_CANCEL(&zclFastPollTimeoutTimerEvt);
			}
			zclFastPollTimeoutTimerEvt = TL_ZB_TIMER_SCHEDULE(app_zclFastPollTimeoutCb, NULL, fastPollTimeoutCnt * POLL_RATE_QUARTERSECONDS);
		}
	}else{
		//continue in normal operation and not required to go into fast poll mode.
	}

	return ZCL_STA_SUCCESS;
}

static status_t app_zclPollCtrlFastPollStopCmdHandler(void)
{
	if(!isFastPollMode){
		return ZCL_STA_ACTION_DENIED;
	}else{
		if(zclFastPollTimeoutTimerEvt){
			TL_ZB_TIMER_CANCEL(&zclFastPollTimeoutTimerEvt);
		}
		app_zclSetFastPollMode(FALSE);
	}

	return ZCL_STA_SUCCESS;
}

static status_t app_zclPollCtrlSetLongPollIntervalCmdHandler(zcl_setLongPollInterval_t *pCmd)
{
	zcl_pollCtrlAttr_t *pPollCtrlAttr = zcl_pollCtrlAttrGet();

	if((pCmd->newLongPollInterval >= 0x04) && (pCmd->newLongPollInterval <= 0x6E0000)
		&& (pCmd->newLongPollInterval <= pPollCtrlAttr->chkInInterval) && (pCmd->newLongPollInterval >= pPollCtrlAttr->shortPollInterval)){
		pPollCtrlAttr->longPollInterval = pCmd->newLongPollInterval;
		zb_setPollRate(pCmd->newLongPollInterval * POLL_RATE_QUARTERSECONDS);
	}else{
		return ZCL_STA_INVALID_VALUE;
	}

	return ZCL_STA_SUCCESS;
}

static status_t app_zclPollCtrlSetShortPollIntervalCmdHandler(zcl_setShortPollInterval_t *pCmd)
{
	zcl_pollCtrlAttr_t *pPollCtrlAttr = zcl_pollCtrlAttrGet();

	if((pCmd->newShortPollInterval >= 0x01) && (pCmd->newShortPollInterval <= 0xff)
		&& (pCmd->newShortPollInterval <= pPollCtrlAttr->longPollInterval)){
		pPollCtrlAttr->shortPollInterval = pCmd->newShortPollInterval;
		zb_setPollRate(pCmd->newShortPollInterval * POLL_RATE_QUARTERSECONDS);
	}else{
		return ZCL_STA_INVALID_VALUE;
	}

	return ZCL_STA_SUCCESS;
}

/*********************************************************************
 * @fn      app_pollCtrlCb
 *
 * @brief   Handler for ZCL Poll Control command.
 *
 * @param   pAddrInfo
 * @param   cmdId
 * @param   cmdPayload
 *
 * @return  status_t
 */
status_t app_pollCtrlCb(zclIncomingAddrInfo_t *pAddrInfo, uint8_t cmdId, void *cmdPayload)
{
	status_t status = ZCL_STA_SUCCESS;

	if(pAddrInfo->dstEp == APP_ENDPOINT){
		if(pAddrInfo->dirCluster == ZCL_FRAME_CLIENT_SERVER_DIR){
			switch(cmdId){
				case ZCL_CMD_CHK_IN_RSP:
					status = app_zclPollCtrlChkInRspCmdHandler((zcl_chkInRsp_t *)cmdPayload);
					break;
				case ZCL_CMD_FAST_POLL_STOP:
					status = app_zclPollCtrlFastPollStopCmdHandler();
					break;
				case ZCL_CMD_SET_LONG_POLL_INTERVAL:
					status = app_zclPollCtrlSetLongPollIntervalCmdHandler((zcl_setLongPollInterval_t *)cmdPayload);
					break;
				case ZCL_CMD_SET_SHORT_POLL_INTERVAL:
					status = app_zclPollCtrlSetShortPollIntervalCmdHandler((zcl_setShortPollInterval_t *)cmdPayload);
					break;
				default:
					break;
			}
		}
	}

	return status;
}
#endif	/* ZCL_POLL_CTRL */

#ifdef ZCL_CO2_MEASUREMENT

status_t app_co2Cb(zclIncomingAddrInfo_t *pAddrInfo, uint8_t cmdId, void *cmdPayload) {

//    printf("app_co2Cb(). pAddrInfo->dirCluster: %0x%x, cmdId: 0x%x\r\n", pAddrInfo->dirCluster, cmdId);

    status_t status = ZCL_STA_SUCCESS;

    return status;
}

#endif /* ZCL_CO2_MEASUREMENT */

/*********************************************************************
 * @fn      app_timeCb
 *
 * @brief   Handler for ZCL Time command.
 *
 * @param   pAddrInfo
 * @param   cmdId
 * @param   cmdPayload
 *
 * @return  status_t
 */
status_t app_timeCb(zclIncomingAddrInfo_t *pAddrInfo, uint8_t cmdId, void *cmdPayload) {

//    printf("app_timeCb. cmd: 0x%x\r\n", cmdId);

    return ZCL_STA_SUCCESS;
}


/*********************************************************************
 * @fn      app_temperatureCb
 *
 * @brief   Handler for ZCL Temperature command.
 *
 * @param   pAddrInfo
 * @param   cmdId
 * @param   cmdPayload
 *
 * @return  status_t
 */
status_t app_temperatureCb(zclIncomingAddrInfo_t *pAddrInfo, uint8_t cmdId, void *cmdPayload) {

//    printf("app_tepmeratureCb. cmd: 0x%x\r\n", cmdId);

    return ZCL_STA_SUCCESS;
}


/*********************************************************************
 * @fn      app_humidityCb
 *
 * @brief   Handler for ZCL Humidity command.
 *
 * @param   pAddrInfo
 * @param   cmdId
 * @param   cmdPayload
 *
 * @return  status_t
 */
status_t app_humidityCb(zclIncomingAddrInfo_t *pAddrInfo, uint8_t cmdId, void *cmdPayload) {

//    printf("app_humidityCb. cmd: 0x%x\r\n", cmdId);

    return ZCL_STA_SUCCESS;
}

/*********************************************************************
 * @fn      app_pressureCb
 *
 * @brief   Handler for ZCL Pressure command.
 *
 * @param   pAddrInfo
 * @param   cmdId
 * @param   cmdPayload
 *
 * @return  status_t
 */
status_t app_pressureCb(zclIncomingAddrInfo_t *pAddrInfo, uint8_t cmdId, void *cmdPayload) {

//    printf("app_pressureCb. cmd: 0x%x\r\n", cmdId);

    return ZCL_STA_SUCCESS;
}

/*********************************************************************
 * @fn      app_illuminanceCb
 *
 * @brief   Handler for ZCL Illuminance command.
 *
 * @param   pAddrInfo
 * @param   cmdId
 * @param   cmdPayload
 *
 * @return  status_t
 */
status_t app_illuminanceCb(zclIncomingAddrInfo_t *pAddrInfo, uint8_t cmdId, void *cmdPayload) {

//    printf("app_illuminanceCb. cmd: 0x%x\r\n", cmdId);

    return ZCL_STA_SUCCESS;
}

/*********************************************************************
 * @fn      app_diagnosticsCb
 *
 * @brief   Handler for ZCL Time command.
 *
 * @param   pAddrInfo
 * @param   cmdId
 * @param   cmdPayload
 *
 * @return  status_t
 */
status_t app_diagnosticsCb(zclIncomingAddrInfo_t *pAddrInfo, uint8_t cmdId, void *cmdPayload) {

    //printf("app_diagnosticsCb. cmd: 0x%x\r\n", cmdId);

    return ZCL_STA_SUCCESS;
}


///***********************************************************************************************************
// * @brief       Send AF data
// *
// * @param[in]   srcEp       - source endpoint
// * @param[in]   pDstEpInfo  - destination information
// * @param[in]   clusterId   - cluster identifier
// * @param[in]   cmdPldLen   - data length
// * @param[in]   cmdPld      - data payload
// * @param[in]   apsCnt      - the APS count
// *
// * @return      Status
// */
//u8 af_dataSend(u8 srcEp, epInfo_t *pDstEpInfo, u16 clusterId, u16 cmdPldLen, u8 *cmdPld, u8 *apsCnt);
//
//void send_lqi_request_to_coordinator()
//{
//    u8 dummy = 0x01; // payload для примера
//
//    af_dataSend(0x0000, // адрес координатора
//                1,      // dst endpoint
//                0x1234, // произвольный cluster ID (например, "LQI request")
//                1,      // длина
//                &dummy,
//                1);     // security enable
//}

int32_t app_diagnostics_cmdCb(void *arg) {


    //printf("app_diagnostics_cmdCb()\r\n");

    if(zb_isDeviceJoinedNwk()) {


        epInfo_t dstEpInfo;
        TL_SETSTRUCTCONTENT(dstEpInfo, 0);

        dstEpInfo.profileId = HA_PROFILE_ID;
//#if FIND_AND_BIND_SUPPORT
//        dstEpInfo.dstAddrMode = APS_DSTADDR_EP_NOTPRESETNT;
//#else
        dstEpInfo.dstAddrMode = APS_SHORT_DSTADDR_WITHEP;
        dstEpInfo.dstEp = APP_ENDPOINT1;
        dstEpInfo.dstAddr.shortAddr = 0x0;
//#endif

        uint8_t apsCnt = 0;
        u8 dummy = 0x01;
        /*u8 ret = */af_dataSend(APP_ENDPOINT1, &dstEpInfo, 0x1234, 1, &dummy, &apsCnt);

        //printf("af_dataSend ret: %d\r\n", ret);

//
//        zclAttrInfo_t *pAttrEntry;
//        pAttrEntry = zcl_findAttribute(APP_ENDPOINT1, ZCL_CLUSTER_GEN_DIAGNOSTICS, ZCL_DIAGNOSTICS_ATTRID_LAST_MESSAGE_LQI);
//
//        zclReadCmd_t *pReadCmd = (zclReadCmd_t *)ev_buf_allocate(sizeof(zclReadCmd_t)+sizeof(uint16_t));
//        if(pReadCmd){
//            pReadCmd->numAttr = 1;
//            pReadCmd->attrID[0] = ZCL_DIAGNOSTICS_ATTRID_LAST_MESSAGE_LQI;
//
//            zcl_read(APP_ENDPOINT1, &dstEpInfo, ZCL_CLUSTER_GEN_DIAGNOSTICS, MANUFACTURER_CODE_NONE, 0, 0, 0, pReadCmd);
//
//            ev_buf_free((uint8_t *)pReadCmd);
//        }

    }

    return 0;
}

/*********************************************************************
 * @fn      app_displayMoveToLevelProcess
 *
 * @brief
 *
 * @param   cmdId
 * @param   cmd
 *
 * @return  None
 */

static void app_displayMoveToLevelProcess(uint8_t endpoint, uint8_t cmdId, moveToLvl_t *cmd) {

    uint16_t len;
    uint8_t min_level, max_level;

    zcl_getAttrVal(APP_ENDPOINT1, ZCL_CLUSTER_GEN_LEVEL_CONTROL, ZCL_ATTRID_LEVEL_MIN_LEVEL, &len, (uint8_t*)&min_level);
    zcl_getAttrVal(APP_ENDPOINT1, ZCL_CLUSTER_GEN_LEVEL_CONTROL, ZCL_ATTRID_LEVEL_MAX_LEVEL, &len, (uint8_t*)&max_level);

    printf("level: %d\r\n", cmd->level);

    if (cmd->level < min_level || cmd->level > max_level) {
        zcl_setAttrVal(APP_ENDPOINT1,
                       ZCL_CLUSTER_GEN_LEVEL_CONTROL,
                       ZCL_ATTRID_LEVEL_CURRENT_LEVEL,
                       (uint8_t*)&config.brightness);
        return;
    }

    printf("level: %d\r\n", cmd->level);

    if (config.brightness != cmd->level) {
        config.brightness = cmd->level;
        config_save();
        led_set_brightness(cmd->level);
        if (!led_flashing())
            led_on(led_get_color());
    }
}


/*********************************************************************
 * @fn      app_displaylevelCb
 *
 * @brief   Handler for ZCL LEVEL command. This function will set LEVEL attribute first.
 *
 * @param   pAddrInfo
 * @param   cmd - level cluster command id
 * @param   cmdPayload
 *
 * @return  status_t
 */

status_t app_displayLevelCb(zclIncomingAddrInfo_t *pAddrInfo, u8 cmdId, void *cmdPayload) {
//    printf("app_displayLevelCb, cmdId: 0x%02x\r\n", cmdId);
    if(pAddrInfo->dstEp == APP_ENDPOINT1) {
        switch(cmdId){
            case ZCL_CMD_LEVEL_MOVE_TO_LEVEL:
            case ZCL_CMD_LEVEL_MOVE_TO_LEVEL_WITH_ON_OFF:
                app_displayMoveToLevelProcess(pAddrInfo->dstEp, cmdId, (moveToLvl_t *)cmdPayload);
                break;
            default:
                break;
        }
    }

    return ZCL_STA_SUCCESS;
}

#ifdef ZCL_ANALOG_INPUT

status_t app_aInputCb(zclIncomingAddrInfo_t *pAddrInfo, uint8_t cmdId, void *cmdPayload) {

//    printf("app_aInputCb(). pAddrInfo->dirCluster: %0x%x, cmdId: 0x%x\r\n", pAddrInfo->dirCluster, cmdId);

    status_t status = ZCL_STA_SUCCESS;

    return status;
}

#endif /* ZCL_ANALOG_INPUT */

status_t app_thermostat_uicCb(zclIncomingAddrInfo_t *pAddrInfo, uint8_t cmdId, void *cmdPayload) {

//    printf("app_thermostatCb(). pAddrInfo->dirCluster: %0x%04x, cmdId: 0x%04x\r\n", pAddrInfo->dirCluster, cmdId);

//    uint8_t *cmdData = (uint8_t*)cmdPayload;

    status_t status = ZCL_STA_SUCCESS;

//    if(pAddrInfo->dstEp == APP_ENDPOINT1) {
//        switch(cmdId) {
//            case ZCL_CMD_UP_OPEN:
//                printf("CMD Open\r\n");
//                remote_cmd_ocs(pAddrInfo->dstEp, cmdId);
//                break;
//            case ZCL_CMD_DOWN_CLOSE:
//                printf("CMD Close\r\n");
//                remote_cmd_ocs(pAddrInfo->dstEp, cmdId);
//                break;
//            case ZCL_CMD_STOP:
//                printf("CMD Stop\r\n");
//                remote_cmd_ocs(pAddrInfo->dstEp, cmdId);
//                break;
//            case ZCL_CMD_GO_TO_LIFT_PERCENTAGE:
//                printf("CMD go to lift percentage. Payload: 0x%x\r\n", *cmdData);
//                if (*cmdData <= 100) remote_cmd_goToLiftPer(pAddrInfo->dstEp, *cmdData);
//                else status = ZCL_STA_INVALID_VALUE;
//                break;
//            default:
//                break;
//        }
//    }


    return status;
}
