slacky1965/air_quality_monitor_zrd/src/app_endpoint_cfg.c

#include "tl_common.h"
#include "zcl_include.h"

#include "app_main.h"

#ifndef ZCL_BASIC_MFG_NAME
#define ZCL_BASIC_MFG_NAME          {6,'T','E','L','I','N','K'}
#endif
#ifndef ZCL_BASIC_MODEL_ID
#define ZCL_BASIC_MODEL_ID          {8,'T','L','S','R','8','2','x','x'}
#endif
#ifndef ZCL_BASIC_SW_BUILD_ID
#define ZCL_BASIC_SW_BUILD_ID       {10,'0','1','2','2','0','5','2','0','1','7'}
#endif

#define R               ACCESS_CONTROL_READ
#define RW              ACCESS_CONTROL_READ | ACCESS_CONTROL_WRITE
#define RR              ACCESS_CONTROL_READ | ACCESS_CONTROL_REPORTABLE
#define RWR             ACCESS_CONTROL_READ | ACCESS_CONTROL_WRITE | ACCESS_CONTROL_REPORTABLE

#define ZCL_UINT8       ZCL_DATA_TYPE_UINT8
#define ZCL_INT8        ZCL_DATA_TYPE_INT8
#define ZCL_UINT16      ZCL_DATA_TYPE_UINT16
#define ZCL_INT16       ZCL_DATA_TYPE_INT16
#define ZCL_UINT32      ZCL_DATA_TYPE_UINT32
#define ZCL_ENUM8       ZCL_DATA_TYPE_ENUM8
#define ZCL_BOOLEAN     ZCL_DATA_TYPE_BOOLEAN
#define ZCL_BITMAP8     ZCL_DATA_TYPE_BITMAP8
#define ZCL_BITMAP16    ZCL_DATA_TYPE_BITMAP16
#define ZCL_CHAR_STR    ZCL_DATA_TYPE_CHAR_STR
#define ZCL_UTC         ZCL_DATA_TYPE_UTC
#define ZCL_SINGLE      ZCL_DATA_TYPE_SINGLE_PREC

/**
 *  @brief Definition for Incoming cluster / Sever Cluster
 */
const uint16_t app_ep1_inClusterList[] = {
    ZCL_CLUSTER_GEN_BASIC,
    ZCL_CLUSTER_GEN_IDENTIFY,
#ifdef ZCL_GROUP
    ZCL_CLUSTER_GEN_GROUPS,
#endif
#ifdef ZCL_SCENE
    ZCL_CLUSTER_GEN_SCENES,
#endif
#ifdef ZCL_ON_OFF
    ZCL_CLUSTER_GEN_ON_OFF_SWITCH_CONFIG,
#endif
#ifdef ZCL_ZLL_COMMISSIONING
    ZCL_CLUSTER_TOUCHLINK_COMMISSIONING,
#endif
#ifdef ZCL_LEVEL_CTRL
    ZCL_CLUSTER_GEN_LEVEL_CONTROL,
#endif
#ifdef ZCL_CO2_MEASUREMENT
    ZCL_CLUSTER_MS_CO2_MEASUREMENT,
#endif
#ifdef ZCL_TEMPERATURE_MEASUREMENT
    ZCL_CLUSTER_MS_TEMPERATURE_MEASUREMENT,
#endif
    ZCL_CLUSTER_MS_RELATIVE_HUMIDITY,
#ifdef ZCL_ILLUMINANCE_MEASUREMENT
    ZCL_CLUSTER_MS_ILLUMINANCE_MEASUREMENT,
#endif
    ZCL_CLUSTER_MS_PRESSURE_MEASUREMENT,
#ifdef ZCL_ANALOG_INPUT
    ZCL_CLUSTER_GEN_ANALOG_INPUT_BASIC,
#endif
    ZCL_CLUSTER_HAVC_USER_INTERFACE_CONFIG,
    ZCL_CLUSTER_GEN_TIME,
    ZCL_CLUSTER_GEN_POWER_CFG,
};

/**
 *  @brief Definition for Outgoing cluster / Client Cluster
 */
const uint16_t app_ep1_outClusterList[] = {
    ZCL_CLUSTER_GEN_TIME,
#ifdef ZCL_OTA
    ZCL_CLUSTER_OTA,
#endif
#ifdef ZCL_TEMPERATURE_MEASUREMENT
    ZCL_CLUSTER_MS_TEMPERATURE_MEASUREMENT,
#endif
    ZCL_CLUSTER_MS_RELATIVE_HUMIDITY,
    ZCL_CLUSTER_GEN_POWER_CFG,
#ifdef ZCL_ZLL_COMMISSIONING
    ZCL_CLUSTER_TOUCHLINK_COMMISSIONING,
#endif
#ifdef ZCL_ON_OFF
    ZCL_CLUSTER_GEN_ON_OFF,
#endif
};

/**
 *  @brief Definition for Server cluster number and Client cluster number
 */
#define APP_EP1_IN_CLUSTER_NUM   (sizeof(app_ep1_inClusterList)/sizeof(app_ep1_inClusterList[0]))
#define APP_EP1_OUT_CLUSTER_NUM  (sizeof(app_ep1_outClusterList)/sizeof(app_ep1_outClusterList[0]))

/**
 *  @brief Definition for simple description for HA profile
 */
const af_simple_descriptor_t app_ep1Desc = {
    HA_PROFILE_ID,                          /* Application profile identifier */
    HA_DEV_SIMPLE_SENSOR,                   /* Application device identifier */
    APP_ENDPOINT1,                          /* Endpoint */
    2,                                      /* Application device version */
    0,                                      /* Reserved */
    APP_EP1_IN_CLUSTER_NUM,                 /* Application input cluster count */
    APP_EP1_OUT_CLUSTER_NUM,                /* Application output cluster count */
    (uint16_t *)app_ep1_inClusterList,      /* Application input cluster list */
    (uint16_t *)app_ep1_outClusterList,     /* Application output cluster list */
};



/* Basic */
zcl_basicAttr_t g_zcl_basicAttrs =
{
    .zclVersion     = 0x03,
    .appVersion     = APP_RELEASE,
    .stackVersion   = (STACK_RELEASE|STACK_BUILD),
    .hwVersion      = HW_VERSION,
    .manuName       = ZCL_BASIC_MFG_NAME,
    .modelId        = ZCL_BASIC_MODEL_ID,
    .dateCode       = ZCL_BASIC_DATE_CODE,
    .powerSource    = POWER_SOURCE_MAINS_1_PHASE,
    .swBuildId      = ZCL_BASIC_SW_BUILD_ID,
    .deviceEnable   = TRUE,
};

const zclAttrInfo_t basic_attrTbl[] =
{
    { ZCL_ATTRID_BASIC_ZCL_VER,             ZCL_UINT8,      R,  (uint8_t*)&g_zcl_basicAttrs.zclVersion  },
    { ZCL_ATTRID_BASIC_APP_VER,             ZCL_UINT8,      R,  (uint8_t*)&g_zcl_basicAttrs.appVersion  },
    { ZCL_ATTRID_BASIC_STACK_VER,           ZCL_UINT8,      R,  (uint8_t*)&g_zcl_basicAttrs.stackVersion},
    { ZCL_ATTRID_BASIC_HW_VER,              ZCL_UINT8,      R,  (uint8_t*)&g_zcl_basicAttrs.hwVersion   },
    { ZCL_ATTRID_BASIC_MFR_NAME,            ZCL_CHAR_STR,   R,  (uint8_t*)g_zcl_basicAttrs.manuName     },
    { ZCL_ATTRID_BASIC_MODEL_ID,            ZCL_CHAR_STR,   R,  (uint8_t*)g_zcl_basicAttrs.modelId      },
    { ZCL_ATTRID_BASIC_DATE_CODE,           ZCL_CHAR_STR,   R,  (uint8_t*)g_zcl_basicAttrs.dateCode     },
    { ZCL_ATTRID_BASIC_POWER_SOURCE,        ZCL_ENUM8,      R,  (uint8_t*)&g_zcl_basicAttrs.powerSource },
    { ZCL_ATTRID_BASIC_DEV_ENABLED,         ZCL_BOOLEAN,    RW, (uint8_t*)&g_zcl_basicAttrs.deviceEnable},
    { ZCL_ATTRID_BASIC_SW_BUILD_ID,         ZCL_CHAR_STR,   R,  (uint8_t*)&g_zcl_basicAttrs.swBuildId   },

    { ZCL_ATTRID_GLOBAL_CLUSTER_REVISION,   ZCL_UINT16,     R,  (uint8_t*)&zcl_attr_global_clusterRevision},

};

#define ZCL_BASIC_ATTR_NUM       sizeof(basic_attrTbl) / sizeof(zclAttrInfo_t)


/* Identify */
zcl_identifyAttr_t g_zcl_identifyAttrs =
{
    .identifyTime   = 0x0000,
};

const zclAttrInfo_t identify_attrTbl[] =
{
    { ZCL_ATTRID_IDENTIFY_TIME,             ZCL_UINT16,     RW, (uint8_t*)&g_zcl_identifyAttrs.identifyTime},

    { ZCL_ATTRID_GLOBAL_CLUSTER_REVISION,   ZCL_UINT16,     R,  (uint8_t*)&zcl_attr_global_clusterRevision},
};

#define ZCL_IDENTIFY_ATTR_NUM           sizeof(identify_attrTbl) / sizeof(zclAttrInfo_t)

#ifdef ZCL_GROUP
/* Group */
zcl_groupAttr_t g_zcl_groupAttrs =
{
    .nameSupport    = 0,
};

const zclAttrInfo_t group_attrTbl[] =
{
    { ZCL_ATTRID_GROUP_NAME_SUPPORT,        ZCL_BITMAP8,    R,  (uint8_t*)&g_zcl_groupAttrs.nameSupport},

    { ZCL_ATTRID_GLOBAL_CLUSTER_REVISION,   ZCL_UINT16,     R,  (uint8_t*)&zcl_attr_global_clusterRevision},
};

#define ZCL_GROUP_ATTR_NUM    sizeof(group_attrTbl) / sizeof(zclAttrInfo_t)

#endif

#ifdef ZCL_SCENE
/* Scene */
zcl_sceneAttr_t g_zcl_sceneAttrs = {
    .sceneCount     = 0,
    .currentScene   = 0,
    .currentGroup   = 0x0000,
    .sceneValid     = FALSE,
    .nameSupport    = 0,
};

const zclAttrInfo_t scene_attrTbl[] = {
    { ZCL_ATTRID_SCENE_SCENE_COUNT,         ZCL_UINT8,      R,  (uint8_t*)&g_zcl_sceneAttrs.sceneCount   },
    { ZCL_ATTRID_SCENE_CURRENT_SCENE,       ZCL_UINT8,      R,  (uint8_t*)&g_zcl_sceneAttrs.currentScene },
    { ZCL_ATTRID_SCENE_CURRENT_GROUP,       ZCL_UINT16,     R,  (uint8_t*)&g_zcl_sceneAttrs.currentGroup },
    { ZCL_ATTRID_SCENE_SCENE_VALID,         ZCL_BOOLEAN,    R,  (uint8_t*)&g_zcl_sceneAttrs.sceneValid   },
    { ZCL_ATTRID_SCENE_NAME_SUPPORT,        ZCL_BITMAP8,    R,  (uint8_t*)&g_zcl_sceneAttrs.nameSupport  },

    { ZCL_ATTRID_GLOBAL_CLUSTER_REVISION,   ZCL_UINT16,     R,  (uint8_t*)&zcl_attr_global_clusterRevision},
};

#define ZCL_SCENE_ATTR_NUM   sizeof(scene_attrTbl) / sizeof(zclAttrInfo_t)

#endif

zcl_timeAttr_t g_zcl_timeAttrs = {
    .time_utc   = 0xffffffff,
    .time_local = 0xffffffff,
    .time_status = 0,
};

const zclAttrInfo_t time_attrTbl[] =
{
    { ZCL_ATTRID_TIME,                      ZCL_UTC,        RWR,    (uint8_t*)&g_zcl_timeAttrs.time_utc         },
    { ZCL_ATTRID_LOCAL_TIME,                ZCL_UINT32,     R,      (uint8_t*)&g_zcl_timeAttrs.time_local       },
    { ZCL_ATTRID_TIME_STATUS,               ZCL_BITMAP8,    RW,     (uint8_t*)&g_zcl_timeAttrs.time_status      },

    { ZCL_ATTRID_GLOBAL_CLUSTER_REVISION,   ZCL_UINT16,     R,      (uint8_t*)&zcl_attr_global_clusterRevision  },
};

#define ZCL_TIME_ATTR_NUM    sizeof(time_attrTbl) / sizeof(zclAttrInfo_t)

zcl_customAttr_t g_zcl_customAttrs = {
        .temperature_offset = 0,                                // -5 <-> +5 * 100
        .read_sensors_period = DEFAULT_READ_SENSORS_PERIOD,
        .co2_onoff = DEFAULT_CO2_ONOFF,
        .co2_onoff_low = DEFAULT_CO2_ONOFF_MIN,
        .co2_onoff_high = DEFAULT_CO2_ONOFF_MAX,
        .voc_onoff = DEFAULT_VOC_ONOFF,
        .voc_onoff_low = DEFAULT_VOC_ONOFF_MIN,
        .voc_onoff_high = DEFAULT_VOC_ONOFF_MAX,
        .co2_frc = 0,
        .display_rotate = DEFAULT_ROTATE,
        .dispaly_inversion = DEFAULT_INVERSION,
        .sound = DEFAULT_SOUND,                                 // 0 - off, 1 - on
};

#ifdef ZCL_CO2_MEASUREMENT

zcl_co2Attr_t g_zcl_co2Attrs = {
        .value = 0.001014,
};


const zclAttrInfo_t co2_attrTbl[] = {
        { ZCL_CO2_MEASUREMENT_ATTRID_MEASUREDVALUE,     ZCL_SINGLE,     RR,     (uint8_t*)&g_zcl_co2Attrs.value                 },
        { ZCL_CO2_MEASUREMENT_ATTRID_MINMEASUREDVALUE,  ZCL_SINGLE,     R,      (uint8_t*)&g_zcl_co2Attrs.min                   },
        { ZCL_CO2_MEASUREMENT_ATTRID_MAXMEASUREDVALUE,  ZCL_SINGLE,     R,      (uint8_t*)&g_zcl_co2Attrs.max                   },
        { ZCL_ATTRID_CMS_CUSTOM_CO2_ONOFF,              ZCL_BOOLEAN,    RWR,    (uint8_t*)&g_zcl_customAttrs.co2_onoff          },
        { ZCL_ATTRID_CMS_CUSTOM_CO2_LOW,                ZCL_UINT16,     RWR,    (uint8_t*)&g_zcl_customAttrs.co2_onoff_low      },
        { ZCL_ATTRID_CMS_CUSTOM_CO2_HIGH,               ZCL_UINT16,     RWR,    (uint8_t*)&g_zcl_customAttrs.co2_onoff_high     },
        { ZCL_ATTRID_CMS_CUSTOM_CO2_FORCED_CALIBRATION, ZCL_INT16,      RWR,    (uint8_t*)&g_zcl_customAttrs.co2_frc            },

        { ZCL_ATTRID_GLOBAL_CLUSTER_REVISION,           ZCL_UINT16, R,  (uint8_t*)&zcl_attr_global_clusterRevision  },
};

#define ZCL_CO2_ATTR_NUM   sizeof(co2_attrTbl) / sizeof(zclAttrInfo_t)

#endif

#ifdef ZCL_TEMPERATURE_MEASUREMENT
zcl_temperatureAttr_t g_zcl_temperatureAttrs = {
        .value = 0x8000,    /* temperature unknown  */
        .minValue = 0xF060, /* -40.00               */
        .maxValue = 0x2134, /* +85.00               */
};


const zclAttrInfo_t temperature_attrTbl[] = {
        { ZCL_TEMPERATURE_MEASUREMENT_ATTRID_MEASUREDVALUE,     ZCL_INT16,  RR,  (uint8_t*)&g_zcl_temperatureAttrs.value         },
        { ZCL_TEMPERATURE_MEASUREMENT_ATTRID_MINMEASUREDVALUE,  ZCL_INT16,  R,   (uint8_t*)&g_zcl_temperatureAttrs.minValue      },
        { ZCL_TEMPERATURE_MEASUREMENT_ATTRID_MAXMEASUREDVALUE,  ZCL_INT16,  R,   (uint8_t*)&g_zcl_temperatureAttrs.maxValue      },
        { ZCL_ATTRID_TMS_CUSTOM_TEMPERATURE_OFFSET,             ZCL_INT16,  RWR, (uint8_t*)&g_zcl_customAttrs.temperature_offset },
        { ZCL_ATTRID_TMS_CUSTOM_READ_SENSORS_PERIOD,            ZCL_UINT16, RWR, (uint8_t*)&g_zcl_customAttrs.read_sensors_period },

        { ZCL_ATTRID_GLOBAL_CLUSTER_REVISION,           ZCL_UINT16, R,  (uint8_t*)&zcl_attr_global_clusterRevision  },
};

#define ZCL_TEMPERATURE_ATTR_NUM   sizeof(temperature_attrTbl) / sizeof(zclAttrInfo_t)
#endif


zcl_humidityAttr_t g_zcl_humidityAttrs = {
        .value = 0xffff,    /* humidity unknown  */
        .minValue = 0x0000,
        .maxValue = 0x2710, /* 100.00              */
};


const zclAttrInfo_t humidity_attrTbl[] = {
        { ZCL_ATTRID_HUMIDITY_MEASUREDVALUE,     ZCL_UINT16, RR, (uint8_t*)&g_zcl_humidityAttrs.value      },
        { ZCL_ATTRID_HUMIDITY_MINMEASUREDVALUE,  ZCL_UINT16, R,  (uint8_t*)&g_zcl_humidityAttrs.minValue   },
        { ZCL_ATTRID_HUMIDITY_MAXMEASUREDVALUE,  ZCL_UINT16, R,  (uint8_t*)&g_zcl_humidityAttrs.maxValue   },

        { ZCL_ATTRID_GLOBAL_CLUSTER_REVISION,           ZCL_UINT16, R,  (uint8_t*)&zcl_attr_global_clusterRevision  },
};

#define ZCL_HUMIDITY_ATTR_NUM   sizeof(humidity_attrTbl) / sizeof(zclAttrInfo_t)

zcl_pressureAttr_t g_zcl_pressureAttrs = {
        .value = 0x8000,    /* pressure unknown  */
        .minValue = 0x8001,
        .maxValue = 0x7fff,
};


const zclAttrInfo_t pressure_attrTbl[] = {
        { ZCL_ATTRID_PRESSURE_MEASUREDVALUE,     ZCL_INT16, RR, (uint8_t*)&g_zcl_pressureAttrs.value      },
        { ZCL_ATTRID_PRESSURE_MINMEASUREDVALUE,  ZCL_INT16, R,  (uint8_t*)&g_zcl_pressureAttrs.minValue   },
        { ZCL_ATTRID_PRESSURE_MAXMEASUREDVALUE,  ZCL_INT16, R,  (uint8_t*)&g_zcl_pressureAttrs.maxValue   },

        { ZCL_ATTRID_GLOBAL_CLUSTER_REVISION,           ZCL_UINT16, R,  (uint8_t*)&zcl_attr_global_clusterRevision  },
};

#define ZCL_PRESSURE_ATTR_NUM   sizeof(pressure_attrTbl) / sizeof(zclAttrInfo_t)


zcl_illuminanceAttr_t g_zcl_illuminanceAttrs = {
        .value = 0,    /* illuminance low  */
        .minValue = 0x0001,
        .maxValue = 0xfffe,
};


const zclAttrInfo_t illuminance_attrTbl[] = {
        { ZCL_ATTRID_MEASURED_VALUE,            ZCL_UINT16, RR, (uint8_t*)&g_zcl_illuminanceAttrs.value     },
        { ZCL_ATTRID_MIN_MEASURED_VALUE,        ZCL_UINT16, R,  (uint8_t*)&g_zcl_illuminanceAttrs.minValue  },
        { ZCL_ATTRID_MAX_MEASURED_VALUE,        ZCL_UINT16, R,  (uint8_t*)&g_zcl_illuminanceAttrs.maxValue  },

        { ZCL_ATTRID_GLOBAL_CLUSTER_REVISION,   ZCL_UINT16, R,  (uint8_t*)&zcl_attr_global_clusterRevision  },
};

#define ZCL_ILLUMINANCE_ATTR_NUM   sizeof(illuminance_attrTbl) / sizeof(zclAttrInfo_t)

#ifdef ZCL_LEVEL_CTRL
/* Level */
zcl_levelAttr_t g_zcl_levelAttrs = {
    .currentLevel = DEFAULT_BRIGHTNESS,
    .minLevel = 0,
    .maxLevel = 0xFF,
    .options  = 1,
};

const zclAttrInfo_t level_attrTbl[] =
{
    { ZCL_ATTRID_LEVEL_CURRENT_LEVEL,       ZCL_UINT8,      RR, (uint8_t*)&g_zcl_levelAttrs.currentLevel    },
    { ZCL_ATTRID_LEVEL_MIN_LEVEL,           ZCL_UINT8,      R,  (uint8_t*)&g_zcl_levelAttrs.minLevel        },
    { ZCL_ATTRID_LEVEL_MAX_LEVEL,           ZCL_UINT8,      R,  (uint8_t*)&g_zcl_levelAttrs.maxLevel        },
    { ZCL_ATTRID_LEVEL_OPTIONS,             ZCL_BITMAP8,    RW, (uint8_t*)&g_zcl_levelAttrs.options         },

    { ZCL_ATTRID_GLOBAL_CLUSTER_REVISION,   ZCL_UINT16,     R,  (u8*)&zcl_attr_global_clusterRevision       },
};

#define ZCL_LEVEL_ATTR_NUM   sizeof(level_attrTbl) / sizeof(zclAttrInfo_t)

#endif

#ifdef ZCL_ANALOG_INPUT

zcl_aInputAttr_t g_zcl_aInputAttrs = {
        .out_of_service = 0,
        .value = 0,
        .status_flag = 0,
        .app_type.index = ZCL_ANALOG_INPUT_ATTRID_TYPE_IDX_VOC,
        .app_type.type = 0x0C,
        .app_type.group = 0,
};

const zclAttrInfo_t aInput_attrTbl[] = {
        { ZCL_ANALOG_INPUT_ATTRID_OUT_OF_SERVICE,   ZCL_BOOLEAN,    RW,     (uint8_t*)&g_zcl_aInputAttrs.out_of_service },
        { ZCL_ANALOG_INPUT_ATTRID_PRESENT_VALUE,    ZCL_SINGLE,     RWR,    (uint8_t*)&g_zcl_aInputAttrs.value          },
        { ZCL_ANALOG_INPUT_ATTRID_STATUS_FLAG,      ZCL_BITMAP8,    RR,     (uint8_t*)&g_zcl_aInputAttrs.status_flag    },
        { ZCL_ANALOG_INPUT_ATTRID_APPLICATION_TYPE, ZCL_UINT32,     R,      (uint8_t*)&g_zcl_aInputAttrs.app_type       },
        { ZCL_ATTRID_AI_CUSTOM_VOC_ONOFF,           ZCL_BOOLEAN,    RWR,    (uint8_t*)&g_zcl_customAttrs.voc_onoff      },
        { ZCL_ATTRID_AI_CUSTOM_VOC_LOW,             ZCL_UINT16,     RWR,    (uint8_t*)&g_zcl_customAttrs.voc_onoff_low  },
        { ZCL_ATTRID_AI_CUSTOM_VOC_HIGH,            ZCL_UINT16,     RWR,    (uint8_t*)&g_zcl_customAttrs.voc_onoff_high  },

        { ZCL_ATTRID_GLOBAL_CLUSTER_REVISION,       ZCL_UINT16,     R,      (uint8_t*)&zcl_attr_global_clusterRevision  },

};

#define ZCL_AINPUT_ATTR_NUM   sizeof(aInput_attrTbl) / sizeof(zclAttrInfo_t)

#endif

zcl_thermostatCfgAttr_t g_zcl_thermostatCfgAttrs = {
    .temperatureDisplayMode = DEFAULT_DISPLAY_MODE,         // 0x00 - °C, 0x01 - °F (Not support)
    .keypadLockout = 0x00,                                  // on off
};


const zclAttrInfo_t thermostat_ui_cfg_attrTbl[] = {
        { ZCL_ATTRID_HVAC_TEMPERATURE_DISPLAY_MODE, ZCL_ENUM8,  RWR,    (uint8_t*)&g_zcl_thermostatCfgAttrs.temperatureDisplayMode },
        { ZCL_ATTRID_HVAC_KEYPAD_LOCKOUT,           ZCL_ENUM8,  RWR,    (uint8_t*)&g_zcl_thermostatCfgAttrs.keypadLockout          },
        { ZCL_ATTRID_HVAC_CUSTOM_FEATURES_SENSORS,  ZCL_ENUM8,  RWR,    (uint8_t*)&g_zcl_customAttrs.features_sensors              },
        { ZCL_ATTRID_HVAC_CUSTOM_DISPLAY_ROTATE  ,  ZCL_ENUM8,  RWR,    (uint8_t*)&g_zcl_customAttrs.display_rotate                },
        { ZCL_ATTRID_HVAC_CUSTOM_DISPLAY_INVERSION, ZCL_ENUM8,  RWR,    (uint8_t*)&g_zcl_customAttrs.dispaly_inversion             },
        { ZCL_ATTRID_HVAC_CUSTOM_SOUND,             ZCL_BOOLEAN,RWR,    (uint8_t*)&g_zcl_customAttrs.sound                         },

        { ZCL_ATTRID_GLOBAL_CLUSTER_REVISION,        ZCL_UINT16, R,     (uint8_t*)&zcl_attr_global_clusterRevision                },
};

#define ZCL_THERMOSTAT_UIC_ATTR_NUM   sizeof(thermostat_ui_cfg_attrTbl) / sizeof(zclAttrInfo_t)


#ifdef ZCL_ON_OFF_SWITCH_CFG
/* On/Off Config */

zcl_onOffSwitchCfgAttr_t g_zcl_onOffSwitchCfgAttrs = {
    .switchType       = ZCL_SWITCH_TYPE_TOGGLE,
    .switchActions    = ZCL_SWITCH_ACTION_OFF_ON,
};

const zclAttrInfo_t onoff_switch_cfg_attrTbl[] =
{
    { ZCL_ATTRID_SWITCH_TYPE,               ZCL_ENUM8,  R,  (u8*)&g_zcl_onOffSwitchCfgAttrs.switchType    },
    { ZCL_ATTRID_SWITCH_ACTION,             ZCL_ENUM8,  RW, (u8*)&g_zcl_onOffSwitchCfgAttrs.switchActions },

    { ZCL_ATTRID_GLOBAL_CLUSTER_REVISION,   ZCL_UINT16, R,  (u8*)&zcl_attr_global_clusterRevision},
};

#define ZCL_ON_OFF_SWITCH_CFG_ATTR_NUM       sizeof(onoff_switch_cfg_attrTbl) / sizeof(zclAttrInfo_t)

#endif //ZCL_ON_OFF_SWITCH_CFG

/**
 *  @brief Definition for simple switch ZCL specific cluster
 */
const zcl_specClusterInfo_t g_appEp1ClusterList[] = {
    {ZCL_CLUSTER_GEN_BASIC,         MANUFACTURER_CODE_NONE, ZCL_BASIC_ATTR_NUM,         basic_attrTbl,          zcl_basic_register,         app_basicCb},
    {ZCL_CLUSTER_GEN_IDENTIFY,      MANUFACTURER_CODE_NONE, ZCL_IDENTIFY_ATTR_NUM,      identify_attrTbl,       zcl_identify_register,      app_identifyCb},
    {ZCL_CLUSTER_GEN_TIME,          MANUFACTURER_CODE_NONE, ZCL_TIME_ATTR_NUM,          time_attrTbl,           zcl_time_register,          app_timeCb},
#ifdef ZCL_GROUP
    {ZCL_CLUSTER_GEN_GROUPS,        MANUFACTURER_CODE_NONE, ZCL_GROUP_ATTR_NUM,         group_attrTbl,          zcl_group_register,         NULL},
#endif
#ifdef ZCL_SCENE
    {ZCL_CLUSTER_GEN_SCENES,        MANUFACTURER_CODE_NONE, ZCL_SCENE_ATTR_NUM,         scene_attrTbl,         zcl_scene_register,         app_sceneCb},
#endif
#ifdef ZCL_CO2_MEASUREMENT
    {ZCL_CLUSTER_MS_CO2_MEASUREMENT, MANUFACTURER_CODE_NONE, ZCL_CO2_ATTR_NUM,          co2_attrTbl,        zcl_co2_measurement_register,   app_co2Cb},
#endif
#ifdef ZCL_TEMPERATURE_MEASUREMENT
    {ZCL_CLUSTER_MS_TEMPERATURE_MEASUREMENT, MANUFACTURER_CODE_NONE, ZCL_TEMPERATURE_ATTR_NUM,  temperature_attrTbl,    zcl_temperature_measurement_register,   app_temperatureCb},
#endif
    {ZCL_CLUSTER_MS_RELATIVE_HUMIDITY, MANUFACTURER_CODE_NONE, ZCL_HUMIDITY_ATTR_NUM,  humidity_attrTbl,    zcl_humidity_measurement_register,   app_humidityCb},
    {ZCL_CLUSTER_MS_PRESSURE_MEASUREMENT, MANUFACTURER_CODE_NONE, ZCL_PRESSURE_ATTR_NUM,  pressure_attrTbl,    zcl_pressure_measurement_register,   app_pressureCb},
    {ZCL_CLUSTER_MS_ILLUMINANCE_MEASUREMENT, MANUFACTURER_CODE_NONE, ZCL_ILLUMINANCE_ATTR_NUM,  illuminance_attrTbl,    zcl_illuminanceMeasure_register,   app_illuminanceCb},
#ifdef ZCL_LEVEL_CTRL
    {ZCL_CLUSTER_GEN_LEVEL_CONTROL, MANUFACTURER_CODE_NONE, ZCL_LEVEL_ATTR_NUM,         level_attrTbl,          zcl_level_register,         app_displayLevelCb},
#endif
#ifdef ZCL_ANALOG_INPUT
    {ZCL_CLUSTER_GEN_ANALOG_INPUT_BASIC, MANUFACTURER_CODE_NONE, ZCL_AINPUT_ATTR_NUM,  aInput_attrTbl,    zcl_analog_input_register,   app_aInputCb},
#endif
    {ZCL_CLUSTER_HAVC_USER_INTERFACE_CONFIG, MANUFACTURER_CODE_NONE, ZCL_THERMOSTAT_UIC_ATTR_NUM, thermostat_ui_cfg_attrTbl, zcl_thermostat_ui_cfg_register, app_thermostat_uicCb},
#ifdef ZCL_ON_OFF_SWITCH_CFG
    {ZCL_CLUSTER_GEN_ON_OFF_SWITCH_CONFIG, MANUFACTURER_CODE_NONE, ZCL_ON_OFF_SWITCH_CFG_ATTR_NUM, onoff_switch_cfg_attrTbl, zcl_onOffSwitchCfg_register, NULL},
#endif
};

uint8_t APP_EP1_CB_CLUSTER_NUM = (sizeof(g_appEp1ClusterList)/sizeof(g_appEp1ClusterList[0]));
