slacky1965/air_quality_monitor_zrd/src/include/app_epd_images.h

#ifndef SRC_INCLUDE_APP_EPD_IMAGES_H_
#define SRC_INCLUDE_APP_EPD_IMAGES_H_

const unsigned char image_zbLogo[72] = { /* 0X00,0X01,0X18,0X00,0X18,0X00, */
0X00,0XFF,0X00,0X03,0XFF,0XC0,0X0F,0XFF,0XF0,0X18,0X00,0X38,0X00,0X00,0X1C,0X3F,
0XFF,0X0C,0X7F,0XFE,0X1E,0X7F,0XFC,0X3E,0XFF,0XF8,0X3F,0XFF,0XF0,0X7F,0XFF,0XE0,
0XFF,0XFF,0XC1,0XFF,0XFF,0X83,0XFF,0XFF,0X07,0XFF,0XFE,0X0F,0XFF,0XFC,0X1F,0XFF,
0X78,0X3F,0XFE,0X78,0X7F,0XFE,0X30,0XFF,0XFC,0X38,0X00,0X00,0X1C,0X00,0X18,0X0F,
0XFF,0XF0,0X03,0XFF,0XC0,0X00,0XFF,0X00,};

const unsigned char image_level0[96] = { /* 0X00,0X01,0X20,0X00,0X18,0X00, */
0X00,0X00,0X00,0X38,0X00,0X00,0X00,0X44,0X00,0X00,0X00,0X44,0X00,0X00,0X00,0X44,
0X00,0X00,0X0E,0X44,0X00,0X00,0X11,0X44,0X00,0X00,0X11,0X44,0X00,0X00,0X11,0X44,
0X00,0X03,0X91,0X44,0X00,0X04,0X51,0X44,0X00,0X04,0X51,0X44,0X00,0X04,0X51,0X44,
0X00,0XE4,0X51,0X44,0X01,0X14,0X51,0X44,0X01,0X14,0X51,0X44,0X01,0X14,0X51,0X44,
0X39,0X14,0X51,0X44,0X45,0X14,0X51,0X44,0X45,0X14,0X51,0X44,0X45,0X14,0X51,0X44,
0X45,0X14,0X51,0X44,0X45,0X14,0X51,0X44,0X45,0X14,0X51,0X44,0X38,0XE3,0X8E,0X38,
};

const unsigned char image_level1[96] = { /* 0X00,0X01,0X20,0X00,0X18,0X00, */
0X00,0X00,0X00,0X38,0X00,0X00,0X00,0X44,0X00,0X00,0X00,0X44,0X00,0X00,0X00,0X44,
0X00,0X00,0X0E,0X44,0X00,0X00,0X11,0X44,0X00,0X00,0X11,0X44,0X00,0X00,0X11,0X44,
0X00,0X03,0X91,0X44,0X00,0X04,0X51,0X44,0X00,0X04,0X51,0X44,0X00,0X04,0X51,0X44,
0X00,0XE4,0X51,0X44,0X01,0X14,0X51,0X44,0X01,0X14,0X51,0X44,0X01,0X14,0X51,0X44,
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

const unsigned char image_battery_75[30] = { /* 0X00,0X01,0X16,0X00,0X0A,0X00, */
0XFF,0XFF,0XF0,0X80,0X00,0X10,0X99,0X98,0X10,0X99,0X98,0X1C,0X99,0X98,0X1C,0X99,
0X98,0X1C,0X99,0X98,0X1C,0X99,0X98,0X10,0X80,0X00,0X10,0XFF,0XFF,0XF0,};

const unsigned char image_battery_100[30] = { /* 0X00,0X01,0X16,0X00,0X0A,0X00, */
0XFF,0XFF,0XF0,0X80,0X00,0X10,0X99,0X99,0X90,0X99,0X99,0X9C,0X99,0X99,0X9C,0X99,
0X99,0X9C,0X99,0X99,0X9C,0X99,0X99,0X90,0X80,0X00,0X10,0XFF,0XFF,0XF0,};

const unsigned char image_sound_on[51] = { /* 0X00,0X01,0X11,0X00,0X11,0X00, */
0X00,0X00,0X00,0X00,0XC0,0X00,0X01,0XD0,0X00,0X03,0XC8,0X00,0X07,0XC4,0X00,0XEF,
0XD2,0X00,0XEF,0XC9,0X00,0XEF,0XC5,0X00,0XEF,0XD4,0X00,0XEF,0XC5,0X00,0XEF,0XC9,
0X00,0XEF,0XD2,0X00,0X07,0XC4,0X00,0X03,0XC8,0X00,0X01,0XD0,0X00,0X00,0XC0,0X00,
0X00,0X00,0X00,};

const unsigned char image_sound_off[51] = { /* 0X00,0X01,0X11,0X00,0X11,0X00, */
0X00,0X00,0X00,0X00,0XC0,0X00,0X01,0XC0,0X00,0X03,0XC0,0X00,0X07,0XC0,0X00,0XEF,
0XC0,0X00,0XEF,0XD9,0X00,0XEF,0XCB,0X00,0XEF,0XC6,0X00,0XEF,0XC6,0X00,0XEF,0XCB,
0X00,0XEF,0XD1,0X80,0X07,0XC0,0X00,0X03,0XC0,0X00,0X01,0XC0,0X00,0X00,0XC0,0X00,
0X00,0X00,0X00,};

#endif /* SRC_INCLUDE_APP_EPD_IMAGES_H_ */
