slacky1965/air_quality_monitor_zrd/src/include/app_endpoint_cfg.h

#ifndef SRC_INCLUDE_APP_ENDPOINT_CFG_H_
#define SRC_INCLUDE_APP_ENDPOINT_CFG_H_

#define APP_ENDPOINT1 0x01
#define APP_ENDPOINT2 0x02
#define APP_ENDPOINT3 0x03
#define APP_ENDPOINT4 0x04
#define APP_ENDPOINT5 0x05

/**
 *  @brief Defined for basic cluster attributes
 */
typedef struct{
    uint8_t  zclVersion;
    uint8_t  appVersion;
    uint8_t  stackVersion;
    uint8_t  hwVersion;
    uint8_t  manuName[ZCL_BASIC_MAX_LENGTH];
    uint8_t  modelId[ZCL_BASIC_MAX_LENGTH];
    uint8_t  dateCode[ZCL_BASIC_MAX_LENGTH];
    uint8_t  powerSource;
    uint8_t  genDevClass;                        //attr 8
    uint8_t  genDevType;                         //attr 9
    uint8_t  deviceEnable;
    uint8_t  swBuildId[ZCL_BASIC_MAX_LENGTH];    //attr 4000
} zcl_basicAttr_t;

/**
 *  @brief Defined for identify cluster attributes
 */
typedef struct{
    uint16_t identifyTime;
}zcl_identifyAttr_t;

/**
 *  @brief Defined for diagnostics cluster attributes
 */
typedef struct{
    uint8_t lastMessageLQI;
}zcl_diagnosticsAttr_t;

/**
 *  @brief Defined for group cluster attributes
 */
typedef struct{
    u8  nameSupport;
}zcl_groupAttr_t;

/**
 *  @brief Defined for scene cluster attributes
 */
typedef struct{
    u8   sceneCount;
    u8   currentScene;
    u8   nameSupport;
    bool sceneValid;
    u16  currentGroup;
}zcl_sceneAttr_t;

/**
 *  @brief Defined for CO2 clusters attributes
 */
typedef struct {
    float   value;
    float   min;
    float   max;
} zcl_co2Attr_t;

/**
 *  @brief Defined for time cluster attributes
 */
typedef struct {
    uint32_t time_utc;
    uint32_t time_local;
    uint8_t  time_status;
} zcl_timeAttr_t;

/**
 *  @brief Defined for tempearute cluster attributes
 */
typedef struct {
    int16_t value;
    int16_t minValue;
    int16_t maxValue;
} zcl_temperatureAttr_t;

/**
 *  @brief Defined for humidity cluster attributes
 */
typedef struct {
    uint16_t value;
    uint16_t minValue;
    uint16_t maxValue;
} zcl_humidityAttr_t;

/**
 *  @brief Defined for pressure cluster attributes
 */
typedef struct {
    int16_t value;
    int16_t minValue;
    int16_t maxValue;
} zcl_pressureAttr_t;

/**
 *  @brief Defined for ILLUMINANCE cluster attributes
 */
typedef struct {
    uint16_t value;
    uint16_t minValue;
    uint16_t maxValue;
} zcl_illuminanceAttr_t;

/**
 *  @brief Defined for level cluster attributes
 */
typedef struct {
    uint8_t     currentLevel;
    uint8_t     minLevel;
    uint8_t     maxLevel;
    uint8_t     options;
} zcl_levelAttr_t;

/**
 *  @brief Defined for analog input clusters attributes
 */
typedef struct __attribute__((packed)) {
    uint32_t    index  :16;    // 0x0200: Vendor VOC (Index Point)
    uint32_t    type   :8;     // 0x0C: Count – Unitless
    uint32_t    group  :8;     // 0x00: Analog Input
} aInput_appType_t;

typedef struct __attribute__((packed)) {
    uint8_t     out_of_service;
    float       value;
    uint8_t     status_flag;
    aInput_appType_t app_type;
} zcl_aInputAttr_t;

/**
 *  @brief Defined for HVAC UI CFG clusters attributes
 */
typedef struct {
    uint8_t     temperatureDisplayMode;         /* 0x00 - °C, 0x01 - °F. Always °C (Not support) */
    uint8_t     keypadLockout;                  /* on off                                        */
} zcl_thermostatCfgAttr_t;

typedef struct {
    int16_t     temperature_offset;             /* - 5 <-> +5 * 100                       */
    uint16_t    read_sensors_period;            /* 10 sec 10-600                          */
    uint8_t     voc_onoff;                      /* 0 - disabled, 1 - enabled              */
    uint16_t    voc_onoff_low;                  /* 50                                     */
    uint16_t    voc_onoff_high;                 /* 500                                    */
    uint8_t     co2_onoff;                      /* 0 - disabled, 1 - enabled              */
    uint16_t    co2_onoff_low;                  /* 400                                    */
    uint16_t    co2_onoff_high;                 /* 2000                                   */
    int16_t     co2_frc;                        /* value FRC forced calibration           */
    uint8_t     display_rotate;                 /* 0 - horizontal, 1 - vertical           */
    uint8_t     dispaly_inversion;              /* 0 - black on white, 1 - white on black */
    features_sensors_t features_sensors;        /* enum in zcl_custom_attr.h file         */
    uint8_t     sound;                          /* 0 - off, 1 - on                        */
} zcl_customAttr_t;

typedef struct {
    u8 switchType;
    u8 switchActions;
} zcl_onOffSwitchCfgAttr_t;


extern uint8_t APP_EP1_CB_CLUSTER_NUM;

#define zcl_sceneAttrGet()          &g_zcl_sceneAttrs
#define zcl_co2AttrGet()            &g_zcl_co2Attrs
#define zcl_temperatureAttrGet()    &g_zcl_temperatureAttrs
#define zcl_humidityAttrGet()       &g_zcl_humidityAttrs
#define zcl_pressureAttrGet()       &g_zcl_pressureAttrs
#define zcl_illuminanceAttrGet()    &g_zcl_illuminanceAttrs
#define zcl_levelAttrGet()          &g_zcl_levelAttrs
#define zcl_aInputAttrGet()         &g_zcl_aInputAttrs
#define zcl_thermostatCfgAttrGet()  &g_zcl_thermostatCfgAttrs
#define zcl_onOffSwitchCfgAttrGet() &g_zcl_onOffSwitchCfgAttrs
#define zcl_timeAttrGet()           &g_zcl_timeAttrs;

/* Attributes */
extern zcl_basicAttr_t g_zcl_basicAttrs;
extern zcl_identifyAttr_t g_zcl_identifyAttrs;
extern zcl_groupAttr_t g_zcl_group1Attrs;
extern zcl_sceneAttr_t g_zcl_scene1Attrs;
extern zcl_co2Attr_t g_zcl_co2Attrs;
extern zcl_temperatureAttr_t g_zcl_temperatureAttrs;
extern zcl_humidityAttr_t g_zcl_humidityAttrs;
extern zcl_levelAttr_t g_zcl_levelAttrs;
extern zcl_thermostatCfgAttr_t g_zcl_thermostatCfgAttrs;
extern zcl_customAttr_t g_zcl_customAttrs;
extern zcl_onOffSwitchCfgAttr_t g_zcl_onOffSwitchCfgAttrs;
extern zcl_timeAttr_t g_zcl_timeAttrs;

//int32_t app_diagnostics_cmdCb(void *arg);

#endif /* SRC_INCLUDE_APP_ENDPOINT_CFG_H_ */
