slacky1965/air_quality_monitor_zrd/src/include/app_time.h

#ifndef SRC_INCLUDE_APP_TIME_H_
#define SRC_INCLUDE_APP_TIME_H_

#define UNIX_TIME_CONST 946684800

#define JD0 2451911-366 // days until 01.01.2001

typedef struct {
    uint16_t year;
    uint8_t month;
    uint8_t day;
    uint8_t wday;
    uint8_t hour;
    uint8_t minute;
    uint8_t second;
} ftime_t;

typedef struct __attribute__((packed)) {
    uint16_t id;
    uint32_t counter;
    uint8_t  crc;
} lifetime_t;

void set_time_sent();
int32_t app_time_cmdCb(void *arg);
bool get_time_sent();
ftime_t *get_ftime(uint32_t counter);
void print_time();
int32_t app_lifetimeCb(void *args);
void lifetime_restore();
void lifetime_save();


#endif /* SRC_INCLUDE_APP_TIME_H_ */
