slacky1965/air_quality_monitor_zrd/src/include/app_sgp40.h

#ifndef SRC_INCLUDE_APP_SGP40_H_
#define SRC_INCLUDE_APP_SGP40_H_

#include "sgp40.h"

uint8_t app_sgp40_init();
uint16_t app_sgp40_get_voc();
void app_sgp40_measurement();

#endif /* SRC_INCLUDE_APP_SGP40_H_ */
