slacky1965/air_quality_monitor_zrd/src/include/app_types.h

#ifndef SRC_INCLUDE_APP_TYPES_H_
#define SRC_INCLUDE_APP_TYPES_H_

#include "types.h"

typedef u8  uint8_t;
typedef s8  int8_t;
typedef char char8_t;
typedef u16 uint16_t;
typedef s16 int16_t;
typedef u32 uint32_t;
typedef s32 int32_t;
typedef u64 uint64_t;
typedef s64 int64_t;

#define S8_C(x)  x
#define U8_C(x)  x
#define S16_C(x) x
#define U16_C(x) x
#define S32_C(x) x
#define U32_C(x) x
#define S64_C(x) x
#define U64_C(x) x


#endif /* SRC_INCLUDE_APP_TYPES_H_ */
