slacky1965/air_quality_monitor_zrd/src/include/app_utility.h

#ifndef SRC_INCLUDE_APP_UTILITY_H_
#define SRC_INCLUDE_APP_UTILITY_H_

/* for clock_time_exceed() */
#define TIMEOUT_TICK_10MS   10*1000         /* timeout 10 ms    */
#define TIMEOUT_TICK_15MS   15*1000         /* timeout 15 ms    */
#define TIMEOUT_TICK_30MS   30*1000         /* timeout 30 ms    */
#define TIMEOUT_TICK_50MS   50*1000         /* timeout 50 ms    */
#define TIMEOUT_TICK_80MS   80*1000         /* timeout 80 ms    */
#define TIMEOUT_TICK_100MS  100*1000        /* timeout 100 ms   */
#define TIMEOUT_TICK_150MS  150*1000        /* timeout 150 ms   */
#define TIMEOUT_TICK_200MS  200*1000        /* timeout 200 ms   */
#define TIMEOUT_TICK_250MS  250*1000        /* timeout 250 ms   */
#define TIMEOUT_TICK_500MS  500*1000        /* timeout 500 ms   */
#define TIMEOUT_TICK_750MS  750*1000        /* timeout 750 ms   */
#define TIMEOUT_TICK_1SEC   1000*1000       /* timeout 1 sec    */
#define TIMEOUT_TICK_2SEC   2*1000*1000     /* timeout 2 sec    */
#define TIMEOUT_TICK_2_5SEC 25*100*1000     /* timeout 2.5 sec  */
#define TIMEOUT_TICK_3SEC   3*1000*1000     /* timeout 3 sec    */
#define TIMEOUT_TICK_5SEC   5*1000*1000     /* timeout 5 sec    */
#define TIMEOUT_TICK_10SEC  10*1000*1000    /* timeout 10 sec   */
#define TIMEOUT_TICK_15SEC  15*1000*1000    /* timeout 15 sec   */
#define TIMEOUT_TICK_30SEC  30*1000*1000    /* timeout 30 sec   */

/* for TL_ZB_TIMER_SCHEDULE() */
#define TIMEOUT_10MS               10       /* timeout 10  ms   */
#define TIMEOUT_20MS               20       /* timeout 20  ms   */
#define TIMEOUT_100MS              100      /* timeout 100 ms   */
#define TIMEOUT_250MS              250      /* timeout 250 ms   */
#define TIMEOUT_500MS              500      /* timeout 900 ms   */
#define TIMEOUT_900MS              900      /* timeout 900 ms   */
#define TIMEOUT_1SEC        1    * 1000     /* timeout 1 sec    */
#define TIMEOUT_1200MS      12   * 100      /* timeout 1.2 sec  */
#define TIMEOUT_2SEC        2    * 1000     /* timeout 2 sec    */
#define TIMEOUT_3SEC        3    * 1000     /* timeout 3 sec    */
#define TIMEOUT_4SEC        4    * 1000     /* timeout 4 sec    */
#define TIMEOUT_5SEC        5    * 1000     /* timeout 5 sec    */
#define TIMEOUT_6SEC        6    * 1000     /* timeout 6 sec    */
#define TIMEOUT_10SEC       10   * 1000     /* timeout 10 sec   */
#define TIMEOUT_15SEC       15   * 1000     /* timeout 15 sec   */
#define TIMEOUT_30SEC       30   * 1000     /* timeout 30 sec   */
#define TIMEOUT_1MIN        60   * 1000     /* timeout 1 min    */
#define TIMEOUT_1MIN30SEC   90   * 1000     /* timeout 1.5 min  */
#define TIMEOUT_2MIN        120  * 1000     /* timeout 2 min    */
#define TIMEOUT_5MIN        300  * 1000     /* timeout 5 min    */
#define TIMEOUT_10MIN       600  * 1000     /* timeout 10 min   */
#define TIMEOUT_15MIN       900  * 1000     /* timeout 15 min   */
#define TIMEOUT_30MIN       1800 * 1000     /* timeout 30 min   */
#define TIMEOUT_60MIN       3600 * 1000     /* timeout 60 min   */
#define TIMEOUT_2HOUR     TIMEOUT_60MIN*2   /* timeout 1 hour   */

void start_message();
int32_t poll_rateAppCb(void *arg);
int32_t delayedMcuResetCb(void *arg);
int32_t delayedFullResetCb(void *arg);
int32_t delayedFactoryResetCb(void *arg);
uint8_t *itoa(int32_t value, uint8_t *ptr);
//char *strcat(char *str1, const char str2);
uint32_t reverse32(uint32_t in);
uint16_t reverse16(uint16_t in);
int32_t int32_from_str(uint8_t *data);
int16_t int16_from_str(uint8_t *data);
char * mystrstr(char * mainStr, char * subStr);
uint8_t set_zcl_str(uint8_t *str_in, uint8_t *str_out, uint8_t len);
uint8_t *digit64toString(uint64_t value);
double log10(double x);
int32_t temperature_convert_CtoF(int16_t temp);

#endif /* SRC_INCLUDE_APP_UTILITY_H_ */
